PETERFEAYEZ-PERO/Smart-Modular-adjustable-DC-PSU/Images gallary/3d pervious images/Screenshot 2026-06-13 041023.png

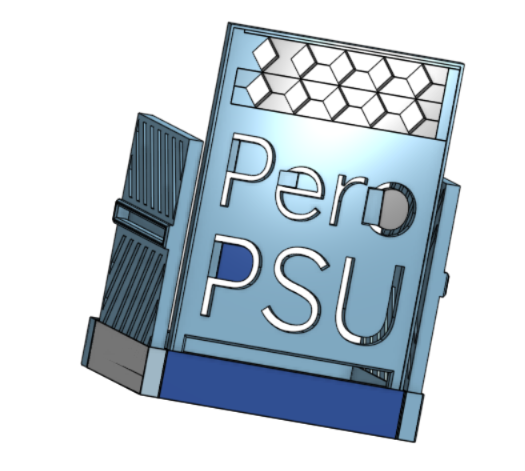
Images gallary/3d pervious images/Screenshot 2026-06-13 041023.png
