PETERFEAYEZ-PERO/Smart-Modular-adjustable-DC-PSU/Images gallary/3d pervious images/Screenshot 2026-06-12 073009.png

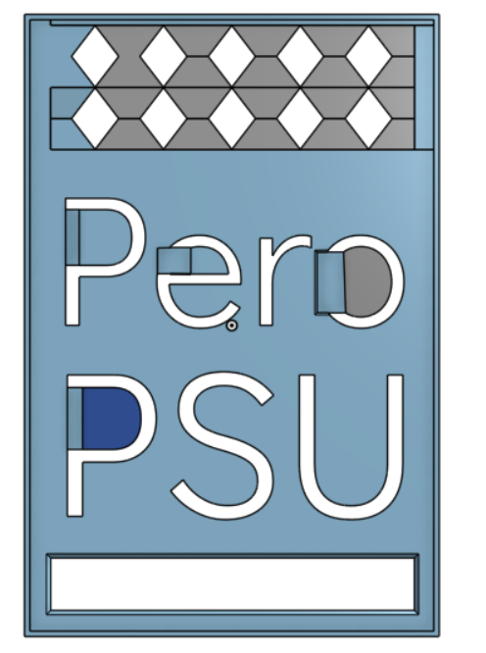
Images gallary/3d pervious images/Screenshot 2026-06-12 073009.png
