PETERFEAYEZ-PERO/Smart-Modular-adjustable-DC-PSU/Images gallary/PCB pervious versions images/Screenshot 2026-05-29 034604.png

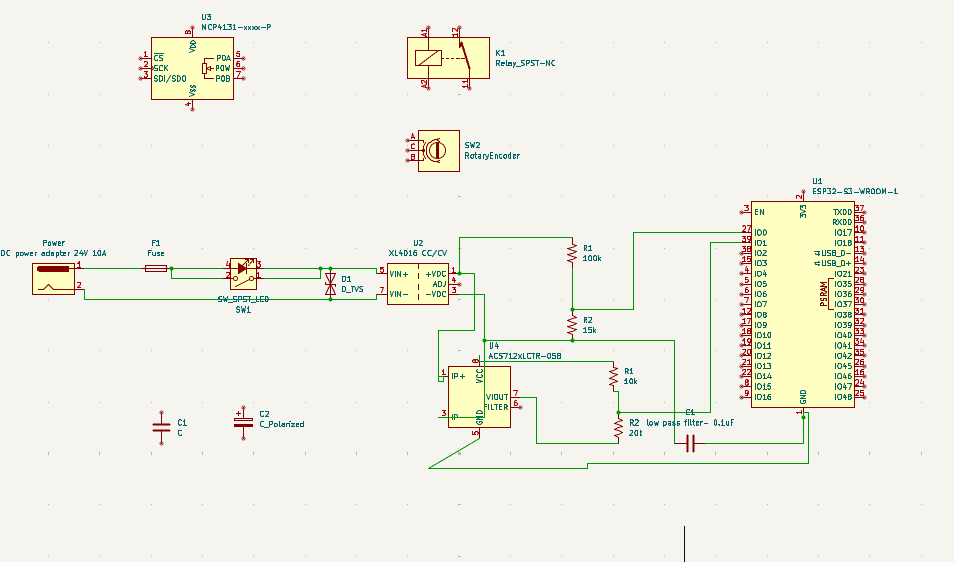
Images gallary/PCB pervious versions images/Screenshot 2026-05-29 034604.png
