PETERFEAYEZ-PERO/Smart-Modular-adjustable-DC-PSU/Images gallary/PCB pervious versions images/Screenshot 2026-06-07 052628 - Copy.png

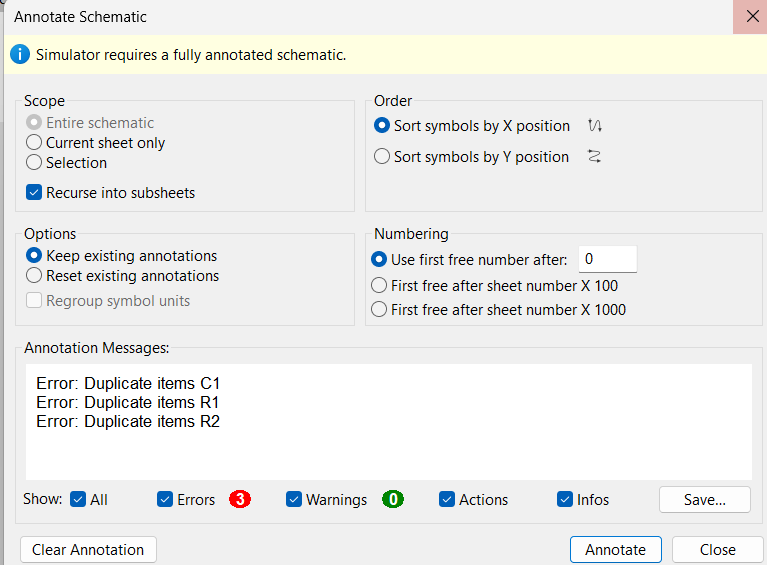
Images gallary/PCB pervious versions images/Screenshot 2026-06-07 052628 - Copy.png
