PETERFEAYEZ-PERO/Smart-Modular-adjustable-DC-PSU/Images gallary/PCB pervious versions images/Screenshot 2026-06-13 090125.png

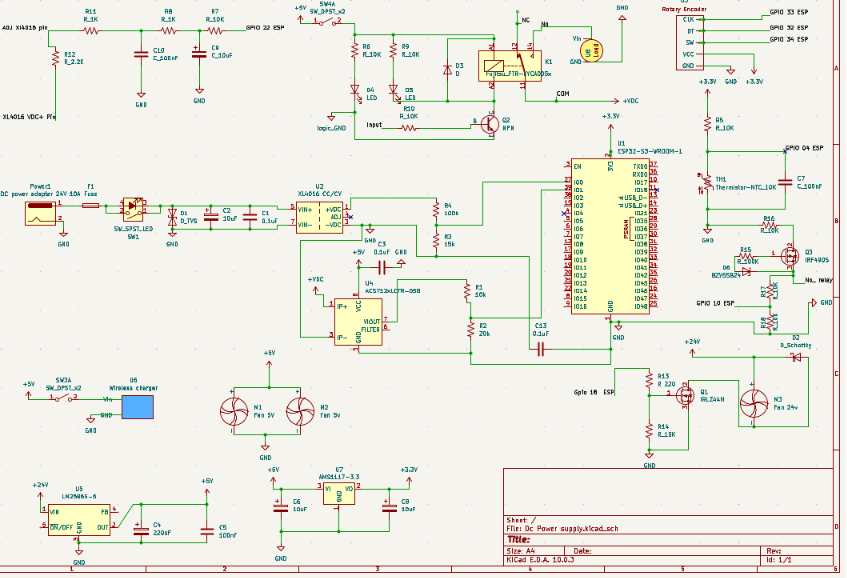
Images gallary/PCB pervious versions images/Screenshot 2026-06-13 090125.png
