PETERFEAYEZ-PERO/Smart-Modular-adjustable-DC-PSU/PCB/USB HUP/USB Hup.kicad_pcb

## KiCad design ereader/audio_headphones.kicad_sch

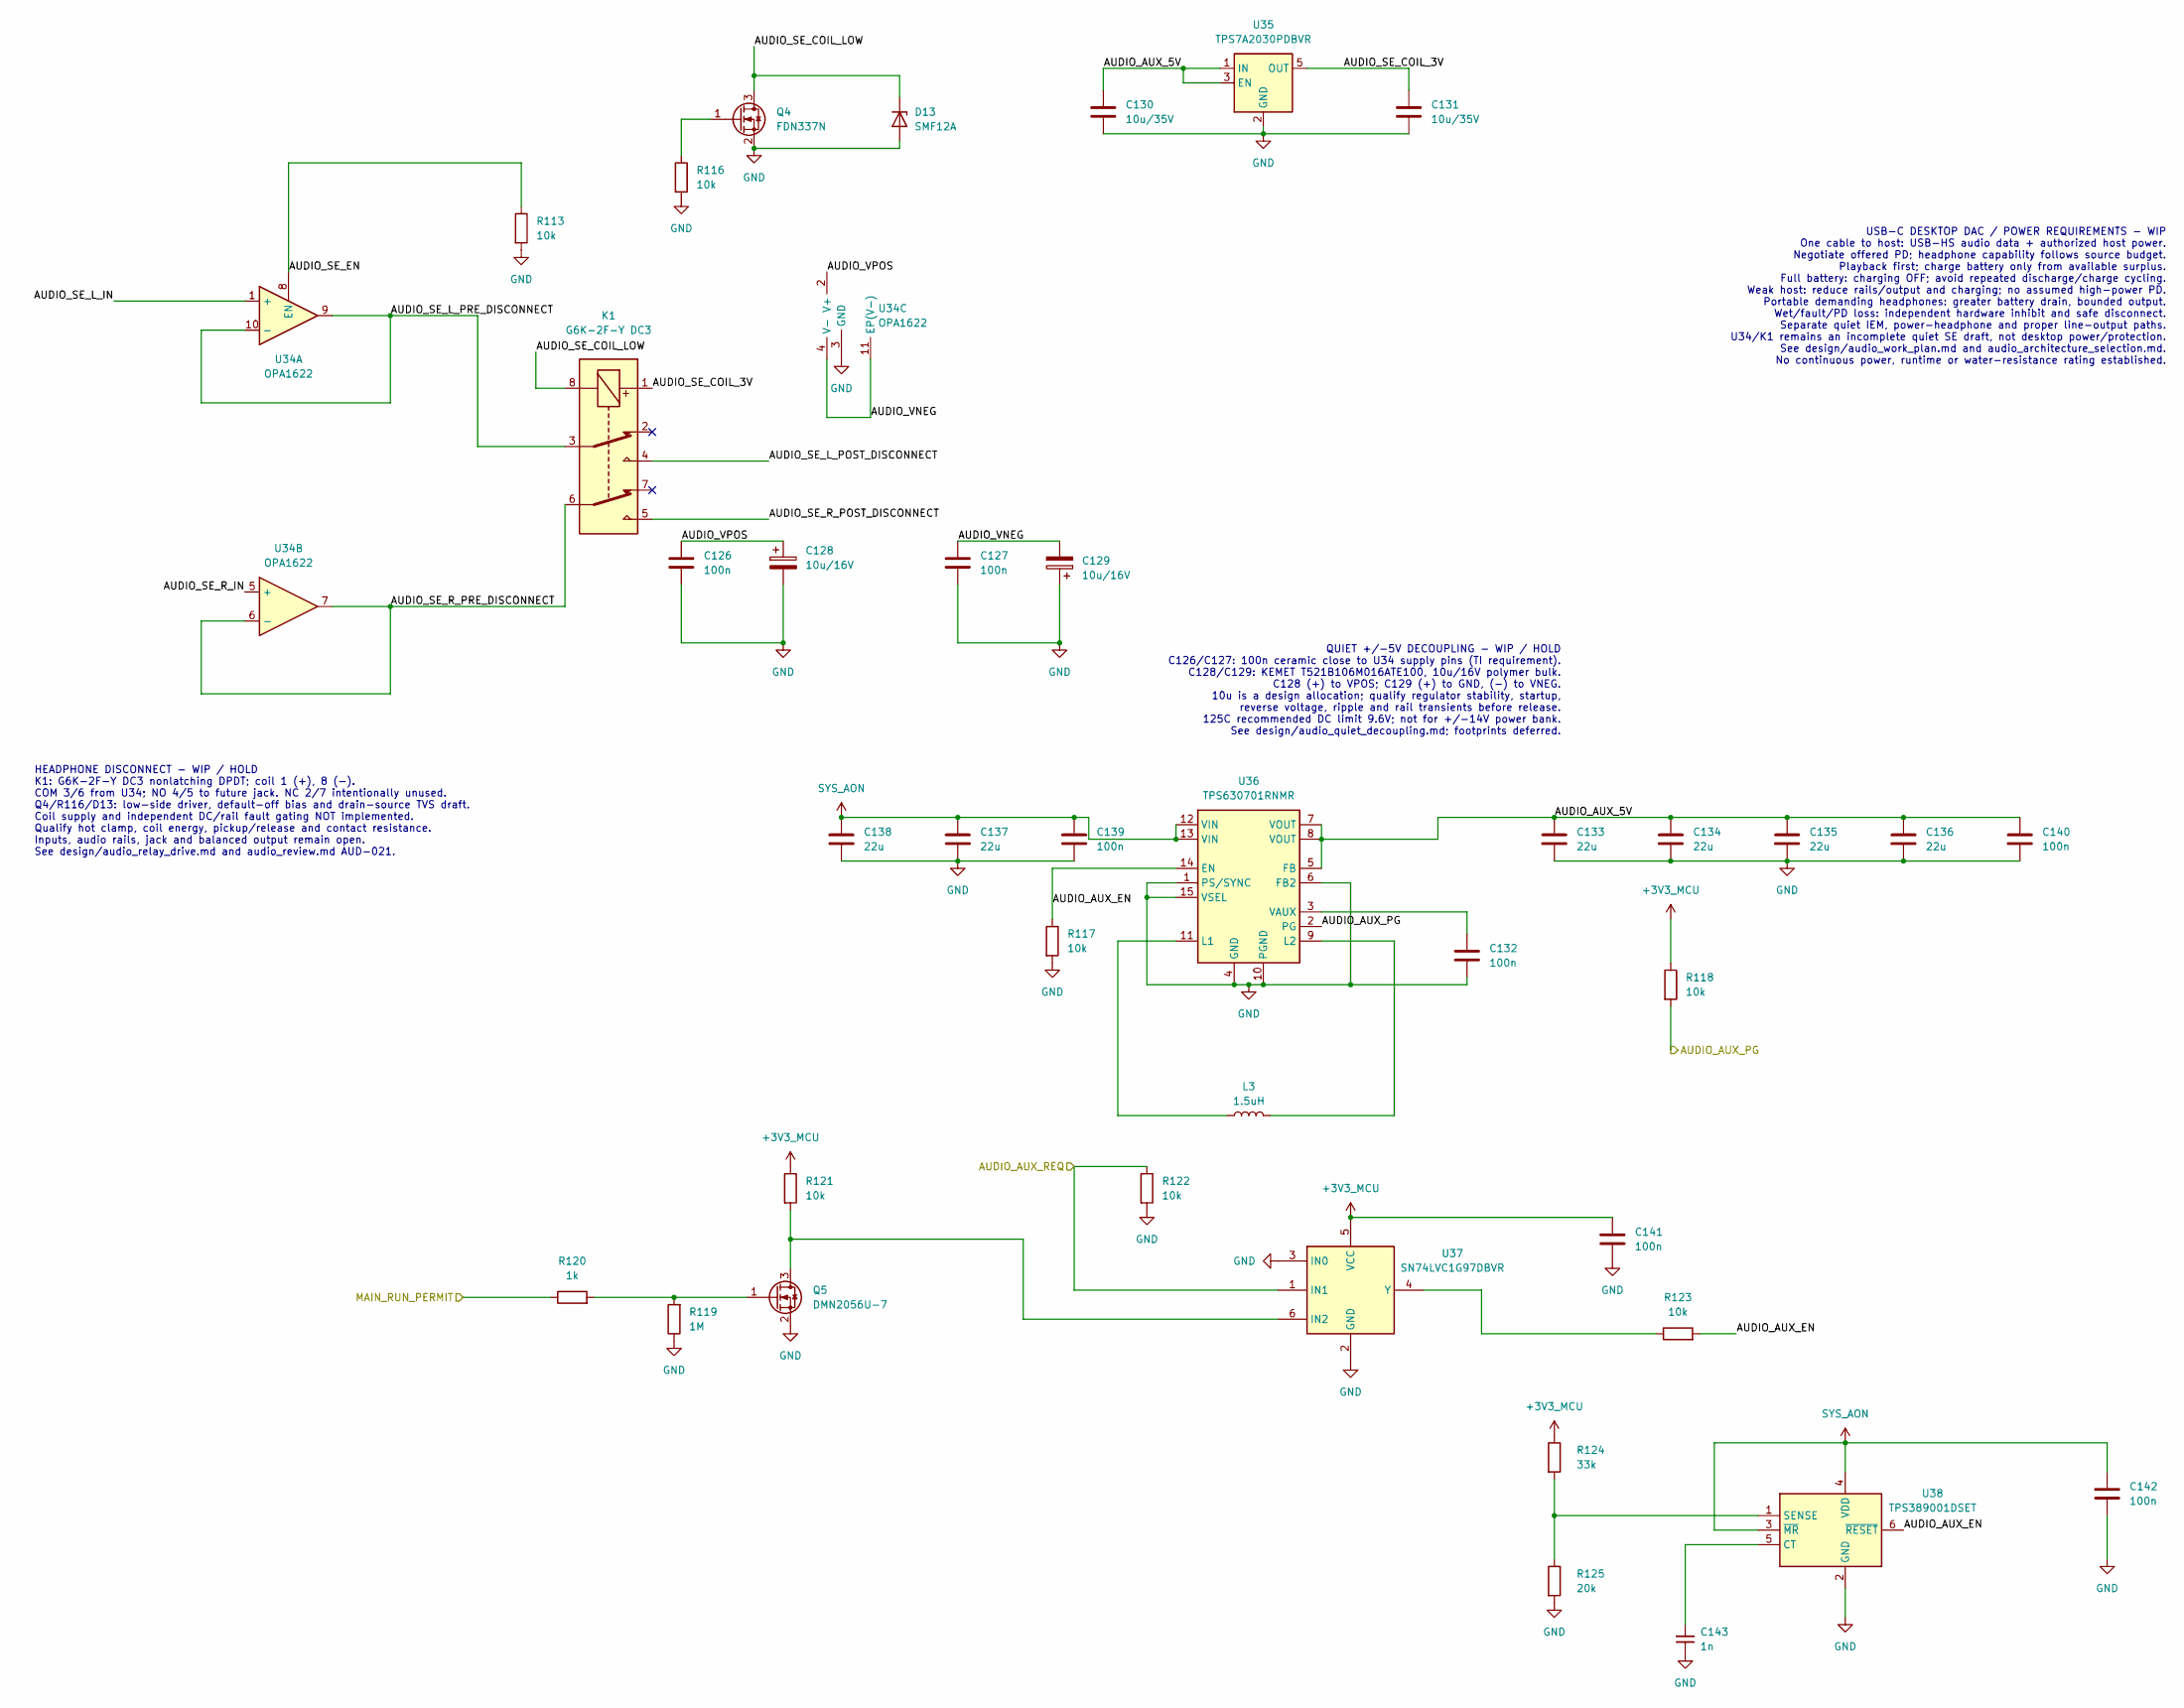
[picture p48: schematic audio_headphones.kicad_sch]

Parts:
C126, C127, C132, C139, C140, C141, C142: 100n; Manufacturer_Part_Number C1608X7R1H104K080AA
C128, C129: 10u/16V; Manufacturer_Part_Number T521B106M016ATE100
C130, C131: 10u/35V
C133, C134, C135, C136, C137, C138: 22u; Manufacturer_Part_Number CL32B226MOJNNNE; DigiKey_Part_Number 1276-3395-1-ND
C143: 1n; Manufacturer_Part_Number C1608NP01H102J080AA; DigiKey_Part_Number 445-14055-1-ND
D13: SMF12A; Manufacturer_Part_Number SMF12A; DigiKey_Part_Number F5747CT-ND
K1: G6K-2F-Y DC3; Manufacturer_Part_Number G6K-2F-Y DC3; DigiKey_Part_Number 39-G6K-2F-YDC3-ND
L3: 1.5uH; Manufacturer_Part_Number XGL4020-152MEC
Q4: FDN337N; Manufacturer_Part_Number FDN337N; DigiKey_Part_Number FDN337NCT-ND
Q5: DMN2056U-7; SOT-23; Manufacturer_Part_Number DMN2056U-7; DigiKey_Part_Number DMN2056U-7DICT-ND
R113, R116, R117, R118, R121, R122, R123: 10k; Manufacturer_Part_Number RC0603FR-0710KL; DigiKey_Part_Number 311-10.0KHRCT-ND
R119: 1M; Manufacturer_Part_Number RC0603FR-071ML; DigiKey_Part_Number 311-1.00MHRCT-ND
R120: 1k; Manufacturer_Part_Number RC0603FR-071KL; DigiKey_Part_Number 311-1.00KHRCT-ND
R124: 33k; Manufacturer_Part_Number ERA-6ARW333V; DigiKey_Part_Number P33KBSCT-ND
R125: 20k; Manufacturer_Part_Number RG1608N-203-W-T1; DigiKey_Part_Number RG16N20.0KWCT-ND
U34: OPA1622; Manufacturer_Part_Number OPA1622IDRCR; DigiKey_Part_Number 296-45038-1-ND
U35: TPS7A2030PDBVR
U36: TPS630701RNMR
U37: SN74LVC1G97DBVR; Manufacturer_Part_Number SN74LVC1G97DBVR; DigiKey_Part_Number 296-15581-1-ND
U38: TPS389001DSET; Manufacturer_Part_Number TPS389001DSET; DigiKey_Part_Number 296-44489-1-ND

Connections:
+3V3_MCU: C141.1, R118.1, R121.1, R124.1, U37.5 (VCC)
AUDIO_AUX_5V: C130.1, C133.1, C134.1, C135.1, C136.1, C140.1, U35.1 (IN), U35.3 (EN), U36.5 (FB), U36.7 (VOUT), U36.8 (VOUT)
AUDIO_AUX_EN: R117.1, R123.2, U36.14 (EN), U38.6 (~RESET)
AUDIO_AUX_PG: R118.2, U36.2 (PG)
AUDIO_AUX_REQ: R122.1, U37.1 (IN1)
AUDIO_SE_COIL_3V: C131.1, K1.1, U35.5 (OUT)
AUDIO_SE_COIL_LOW: D13.1 (K), K1.8, Q4.3 (D)
AUDIO_SE_EN: R113.1, U34.8 (EN)
AUDIO_SE_L_IN: U34.1 (+)
AUDIO_SE_L_POST_DISCONNECT: K1.4
AUDIO_SE_L_PRE_DISCONNECT: K1.3, U34.9, U34.10 (-)
AUDIO_SE_R_IN: U34.5 (+)
AUDIO_SE_R_POST_DISCONNECT: K1.5
AUDIO_SE_R_PRE_DISCONNECT: K1.6, U34.6 (-), U34.7
AUDIO_VNEG: C127.1, C129.2, U34.4 (V-), U34.11 (EP(V-))
AUDIO_VPOS: C126.1, C128.1, U34.2 (V+)
GND: C126.2, C127.2, C128.2, C129.1, C130.2, C131.2, C132.2, C133.2, C134.2, C135.2, C136.2, C137.2, C138.2, C139.2, C140.2, C141.2, C142.2, C143.1, D13.2 (A), Q4.2 (S), Q5.2 (S), R113.2, R116.2, R117.2, R119.1, R122.2, R125.2, U34.3 (GND), U35.2 (GND), U36.1 (PS/SYNC), U36.4 (GND), U36.6 (FB2), U36.10 (PGND), U36.15 (VSEL), U37.2 (GND), U37.3 (IN0), U38.2 (GND)
MAIN_RUN_PERMIT: R120.1
unnamed: C132.1, U36.3 (VAUX)
unnamed: C143.2, U38.5 (CT)
unnamed: L3.1, U36.11 (L1)
unnamed: L3.2, U36.9 (L2)
unnamed: Q4.1 (G), R116.1
unnamed: Q5.1 (G), R119.2, R120.2
unnamed: Q5.3 (D), R121.2, U37.6 (IN2)
unnamed: R123.1, U37.4 (Y)
unnamed: R124.2, R125.1, U38.1 (SENSE)
SYS_AON: C137.1, C138.1, C139.1, C142.1, U36.12 (VIN), U36.13 (VIN), U38.3 (~MR), U38.4 (VDD)

Notes on the sheet:
HEADPHONE DISCONNECT - WIP / HOLD K1: G6K-2F-Y DC3 nonlatching DPDT; coil 1 (+), 8 (-). COM 3/6 from U34; NO 4/5 to future jack. NC 2/7 intentionally unused. Q4/R116/D13: low-side driver, default-off bias and drain-source TVS draft. Coil supply and independent DC/rail fault gating NOT implemented. 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
QUIET +/-5V DECOUPLING - WIP / HOLD C126/C127: 100n ceramic close to U34 supply pins (TI requirement). C128/C129: KEMET T521B106M016ATE100, 10u/16V polymer bulk. C128 (+) to VPOS; C129 (+) to GND, (-) to VNEG. 10u is a design allocation; qualify regulator stability, startup, reverse voltage, ripple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
USB-C DESKTOP DAC / POWER REQUIREMENTS - WIP One cable to host: USB-HS audio data + authorized host power. Negotiate offered PD; headphone capability follows source budget. Playback first; charge battery only from available surplus. Full battery: charging OFF; avoid repeated discharge/charge cyclin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
