PETERFEAYEZ-PERO/Smart-Modular-adjustable-DC-PSU/PCB/USB HUP/USB Hup.kicad_pcb

## KiCad design ereader/camera.kicad_sch

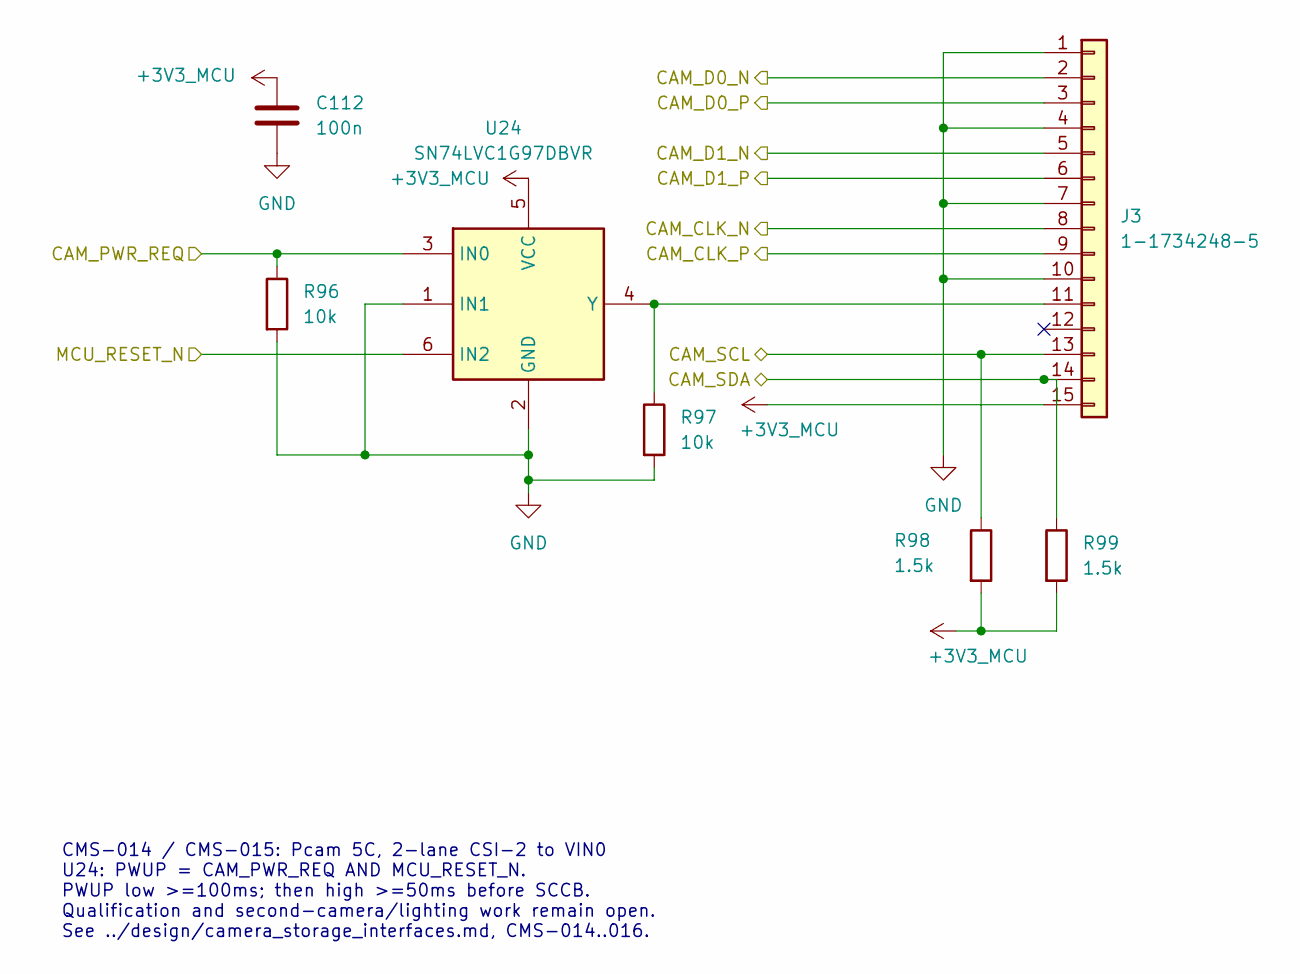
[picture p49: schematic camera.kicad_sch]

Parts:
C112: 100n; Manufacturer_Part_Number C1608X7R1H104K080AA; DigiKey_Part_Number 445-1314-1-ND
J3: 1-1734248-5; Manufacturer_Part_Number 1-1734248-5; DigiKey_Part_Number A101418CT-ND
R96, R97: 10k; Manufacturer_Part_Number RC0603FR-0710KL; DigiKey_Part_Number 311-10.0KHRCT-ND
R98, R99: 1.5k; Manufacturer_Part_Number RC0603FR-071K5L; DigiKey_Part_Number 311-1.50KHRCT-ND
U24: SN74LVC1G97DBVR; Manufacturer_Part_Number SN74LVC1G97DBVR; DigiKey_Part_Number 296-15581-1-ND

Connections:
+3V3_MCU: C112.1, J3.15, R98.2, R99.2, U24.5 (VCC)
CAM_CLK_N: J3.8
CAM_CLK_P: J3.9
CAM_D0_N: J3.2
CAM_D0_P: J3.3
CAM_D1_N: J3.5
CAM_D1_P: J3.6
CAM_PWR_REQ: R96.1, U24.3 (IN0)
CAM_SCL: J3.13, R98.1
CAM_SDA: J3.14, R99.1
GND: C112.2, J3.1, J3.4, J3.7, J3.10, R96.2, R97.2, U24.1 (IN1), U24.2 (GND)
MCU_RESET_N: U24.6 (IN2)
unnamed: J3.11, R97.1, U24.4 (Y)

Notes on the sheet:
CMS-014 / CMS-015: Pcam 5C, 2-lane CSI-2 to VIN0 U24: PWUP = CAM_PWR_REQ AND MCU_RESET_N. PWUP low >=100ms; then high >=50ms before SCCB. Qualification and second-camera/lighting work remain open. See ../design/camera_storage_interfaces.md, CMS-014..016.
