PETERFEAYEZ-PERO/Smart-Modular-adjustable-DC-PSU/PCB/USB HUP/USB Hup.kicad_pcb

## KiCad design ereader/main_3v3_supply.kicad_sch

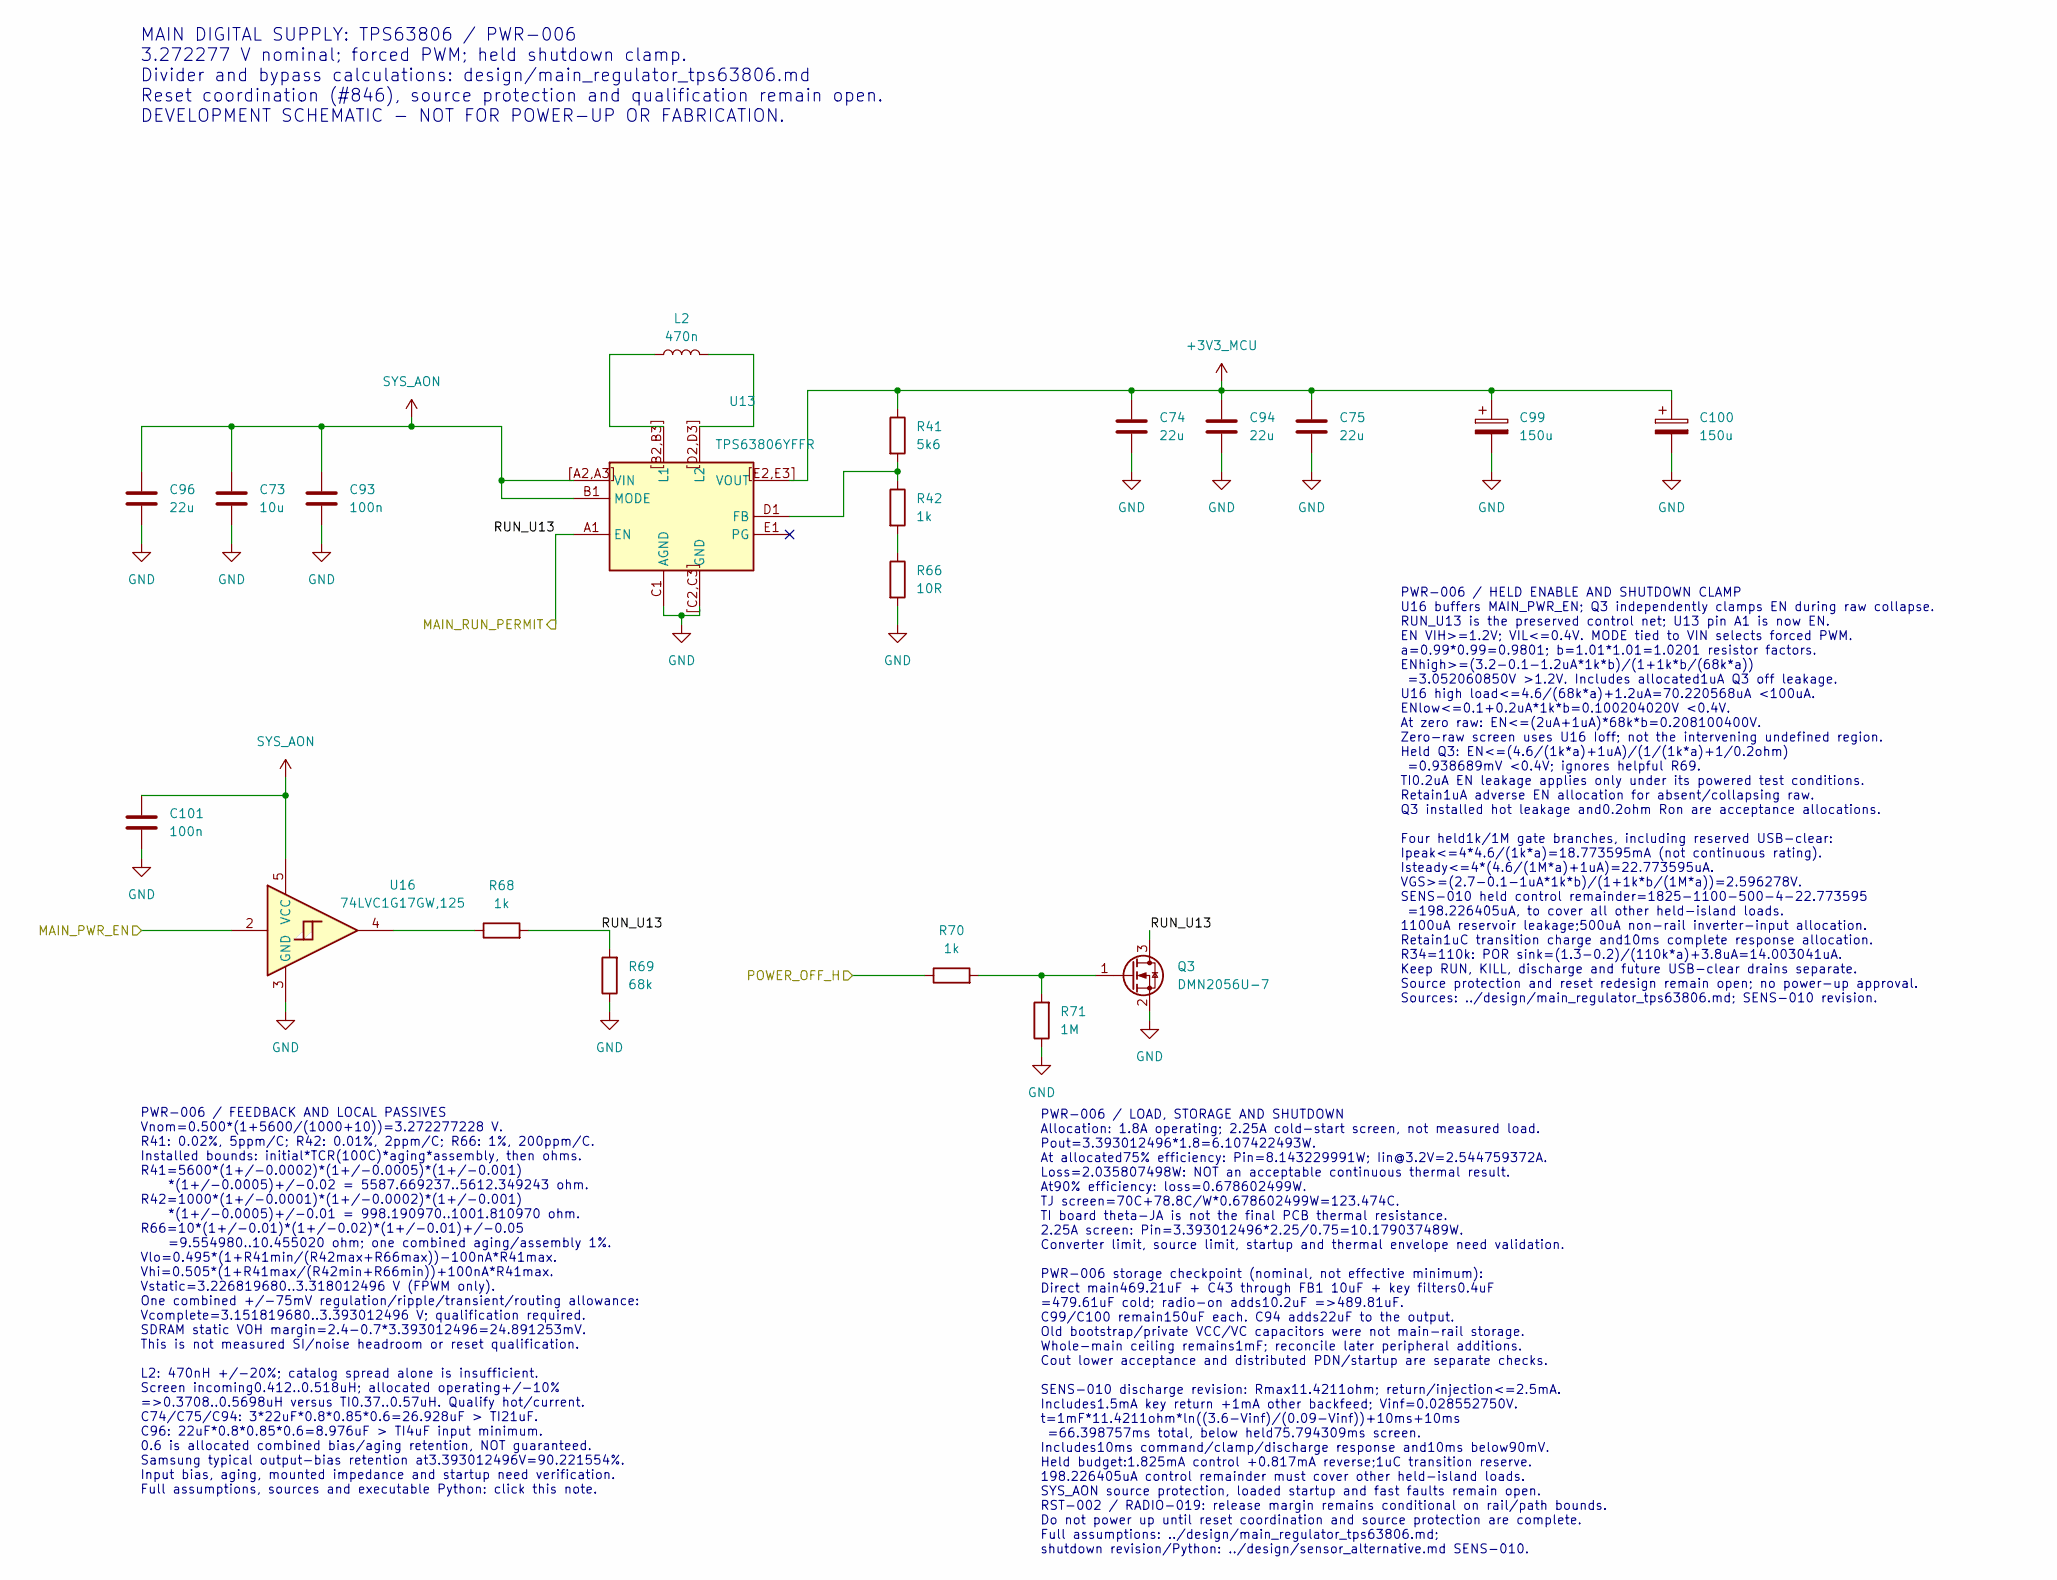
[picture p50: schematic main_3v3_supply.kicad_sch]

Parts:
C73: 10u; Manufacturer_Part_Number C3216X7R1V106K160AC; DigiKey_Part_Number 445-14799-1-ND
C74, C75, C94, C96: 22u; Manufacturer_Part_Number CL32B226MOJNNNE; DigiKey_Part_Number 1276-3395-1-ND
C93, C101: 100n; Manufacturer_Part_Number C1608X7R1H104K080AA; DigiKey_Part_Number 445-1314-1-ND
C99, C100: 150u; Manufacturer_Part_Number EEF-JX0J151RF; DigiKey_Part_Number 10-EEF-JX0J151RFCT-ND
L2: 470n; Manufacturer_Part_Number XGL5020-471MEC; DigiKey_Part_Number 2457-XGL5020-471MEC-ND
Q3: DMN2056U-7; SOT-23; Manufacturer_Part_Number DMN2056U-7; DigiKey_Part_Number DMN2056U-7DICT-ND
R41: 5k6; Manufacturer_Part_Number RG2012V-562-P-T1; DigiKey_Part_Number 408-RG2012V-562-P-T1CT-ND
R42: 1k; Manufacturer_Part_Number RG2012L-102-L-T05; DigiKey_Part_Number 408-1631-1-ND
R66: 10R; Manufacturer_Part_Number RC0603FR-0710RL; DigiKey_Part_Number 311-10.0HRCT-ND
R68, R70: 1k; Manufacturer_Part_Number RC0603FR-071KL; DigiKey_Part_Number 311-1.00KHRCT-ND
R69: 68k; Manufacturer_Part_Number RC0603FR-0768KL; DigiKey_Part_Number 311-68.0KHRCT-ND
R71: 1M; Manufacturer_Part_Number RC0603FR-071ML; DigiKey_Part_Number 311-1.00MHRCT-ND
U13: TPS63806YFFR; Manufacturer_Part_Number TPS63806YFFR; DigiKey_Part_Number 296-TPS63806YFFRCT-ND
U16: 74LVC1G17GW,125; Manufacturer_Part_Number 74LVC1G17GW,125; DigiKey_Part_Number 1727-4117-1-ND

Connections:
+3V3_MCU: C74.1, C75.1, C94.1, C99.1, C100.1, R41.1, U13.[E2,E3] (VOUT)
GND: C73.2, C74.2, C75.2, C93.2, C94.2, C96.2, C99.2, C100.2, C101.2, Q3.2 (S), R66.2, R69.1, R71.1, U13.C1 (AGND), U13.[C2,C3] (GND), U16.3 (GND)
MAIN_PWR_EN: U16.2
MAIN_RUN_PERMIT: Q3.3 (D), R68.2, R69.2, U13.A1 (EN)
unnamed: L2.1, U13.[B2,B3] (L1)
unnamed: L2.2, U13.[D2,D3] (L2)
unnamed: Q3.1 (G), R70.2, R71.2
unnamed: R41.2, R42.1, U13.D1 (FB)
unnamed: R42.2, R66.1
unnamed: R68.1, U16.4
POWER_OFF_H: R70.1
SYS_AON: C73.1, C93.1, C96.1, C101.1, U13.B1 (MODE), U13.[A2,A3] (VIN), U16.5 (VCC)

Notes on the sheet:
PWR-006 / LOAD, STORAGE AND SHUTDOWN Allocation: 1.8A operating; 2.25A cold-start screen, not measured load. Pout=3.393012496*1.8=6.107422493W. At allocated75% efficiency: Pin=8.143229991W; Iin@3.2V=2.544759372A. Loss=2.035807498W: NOT an acceptable continuous thermal result. At90% efficiency: loss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
PWR-006 / HELD ENABLE AND SHUTDOWN CLAMP U16 buffers MAIN_PWR_EN; Q3 independently clamps EN during raw collapse. RUN_U13 is the preserved control net; U13 pin A1 is now EN. EN VIH>=1.2V; VIL<=0.4V. MODE tied to VIN selects forced PWM. a=0.99*0.99=0.9801; b=1.01*1.01=1.0201 resistor factors. ENhigh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
MAIN DIGITAL SUPPLY: TPS63806 / PWR-006 3.272277 V nominal; forced PWM; held shutdown clamp. Divider and bypass calculations: design/main_regulator_tps63806.md Reset coordination (#846), source protection and qualification remain open. DEVELOPMENT SCHEMATIC - NOT FOR POWER-UP OR FABRICATION.
PWR-006 / FEEDBACK AND LOCAL PASSIVES Vnom=0.500*(1+5600/(1000+10))=3.272277228 V. R41: 0.02%, 5ppm/C; R42: 0.01%, 2ppm/C; R66: 1%, 200ppm/C. Installed bounds: initial*TCR(100C)*aging*assembly, then ohms. R41=5600*(1+/-0.0002)*(1+/-0.0005)*(1+/-0.001) *(1+/-0.0005)+/-0.02 = 5587.669237..5612.349243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
