PETERFEAYEZ-PERO/Smart-Modular-adjustable-DC-PSU/PCB/USB HUP/USB Hup.kicad_pcb

## KiCad design ereader/mcu_core_power.kicad_sch

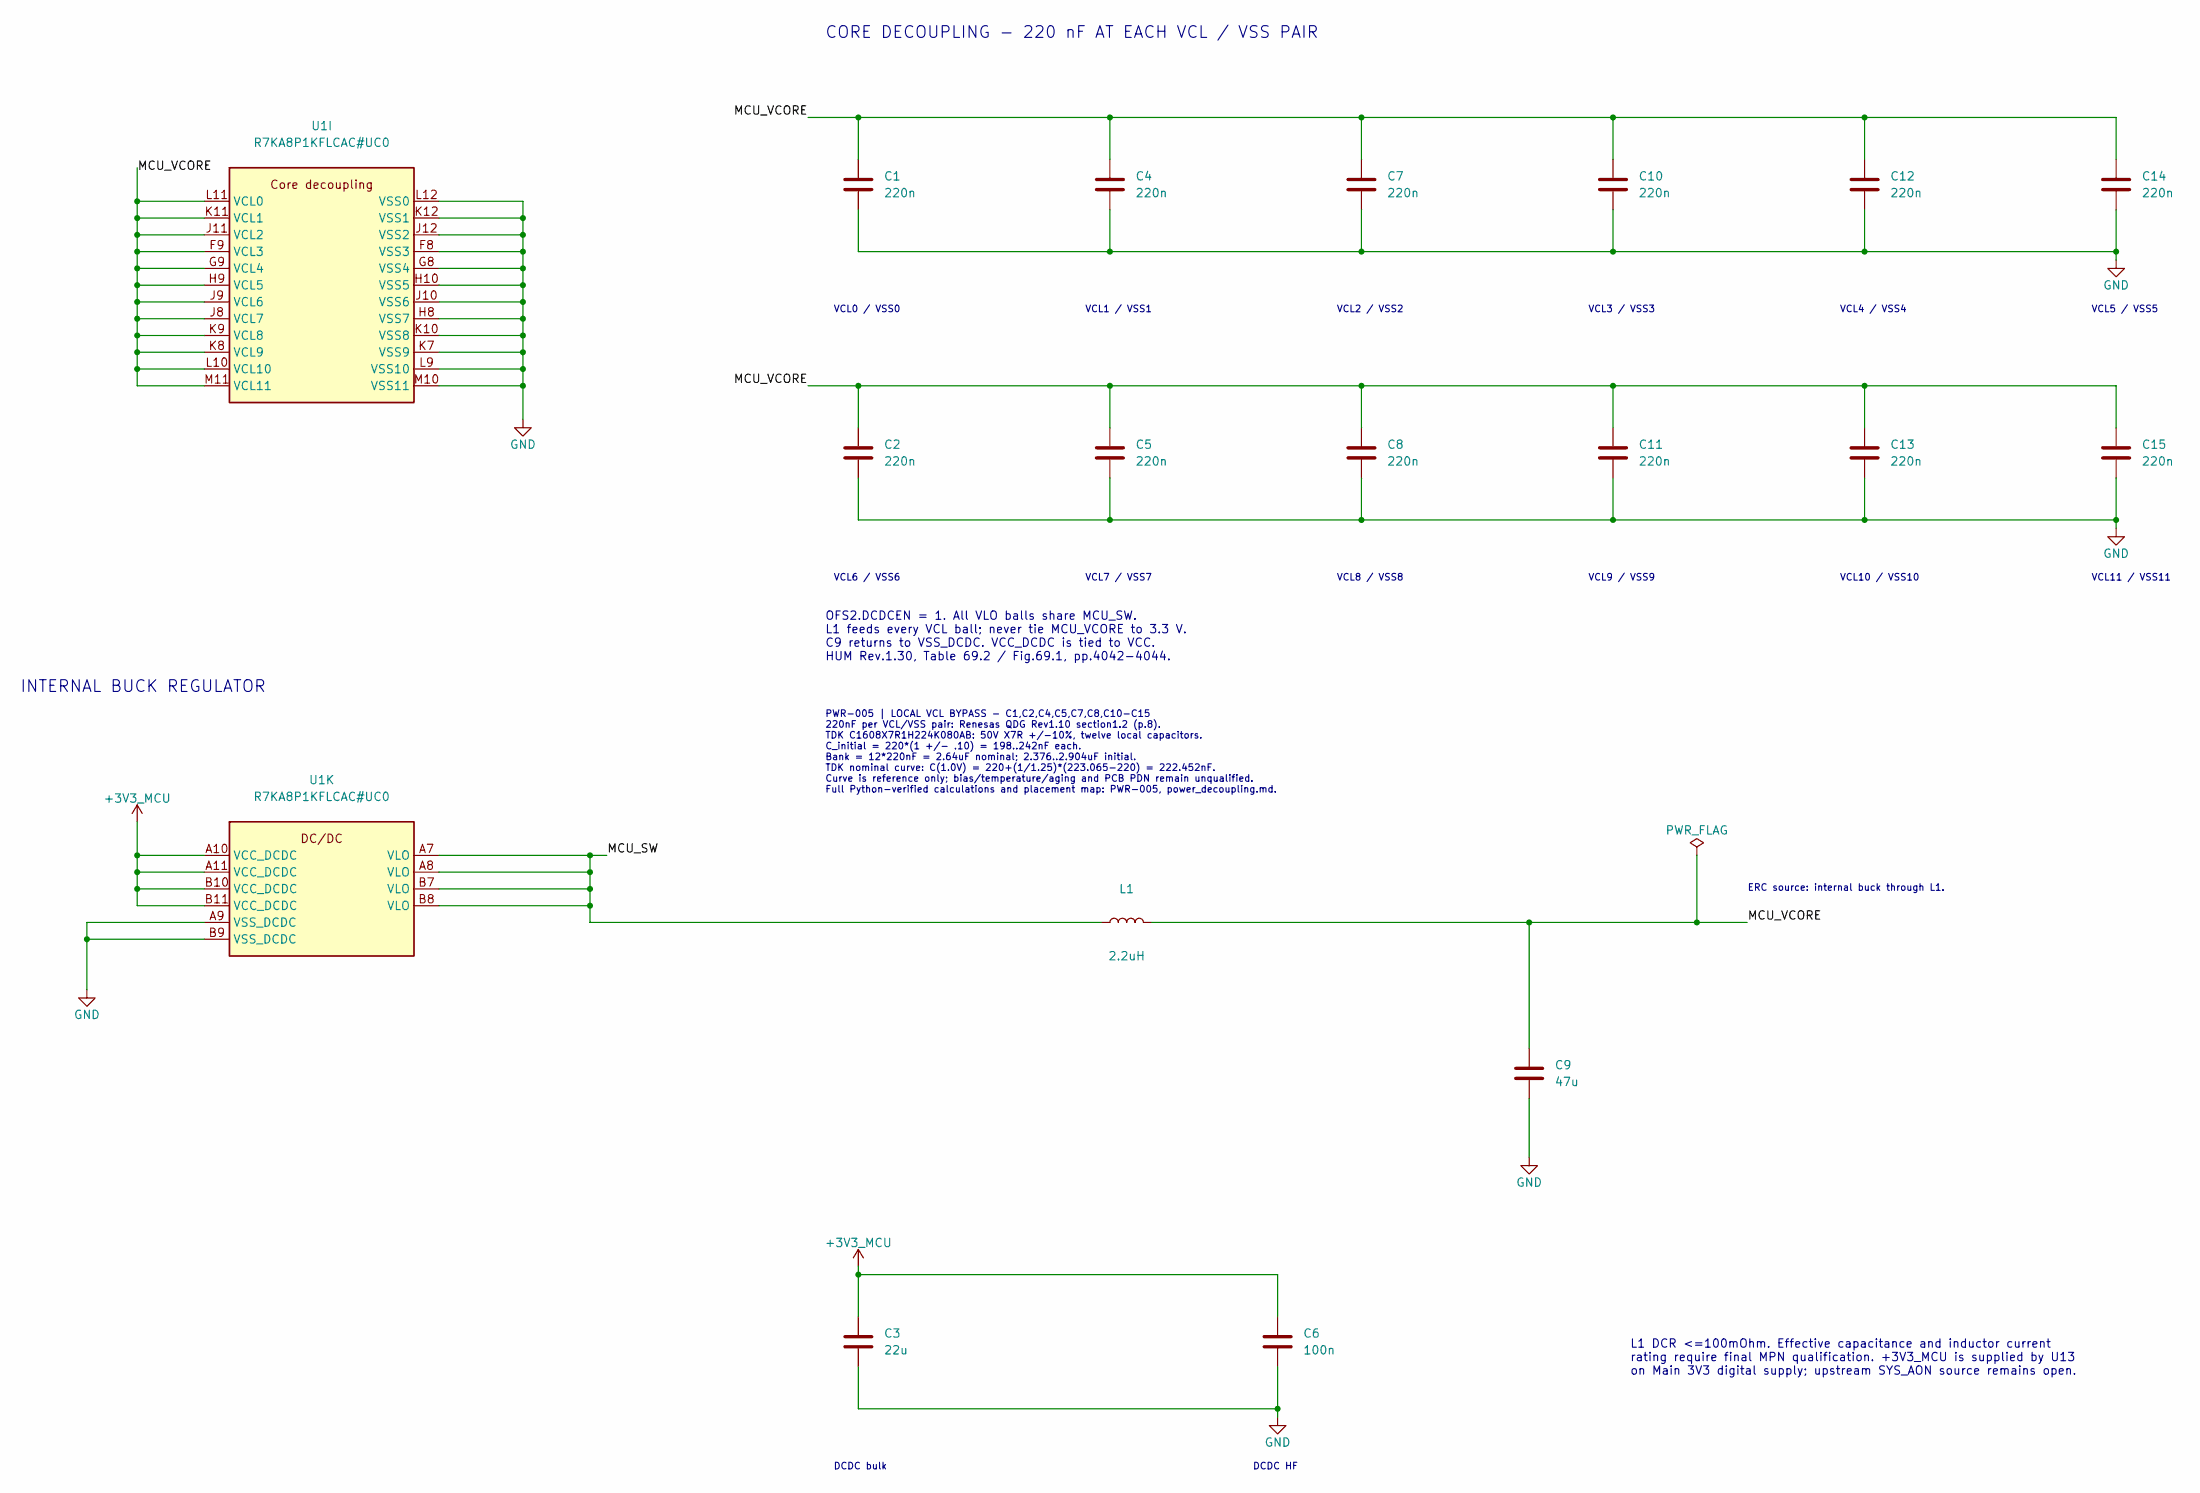
[picture p52: schematic mcu_core_power.kicad_sch]

Parts:
C1, C2, C4, C5, C7, C8, C10, C11, C12, C13, C14, C15: 220n; Manufacturer_Part_Number C1608X7R1H224K080AB; DigiKey_Part_Number 445-7408-1-ND
C3: 22u; Manufacturer_Part_Number GRM31CR70J226KE19L; DigiKey_Part_Number 490-6515-1-ND
C6: 100n; Manufacturer_Part_Number C1608X7R1H104K080AA; DigiKey_Part_Number 445-1314-1-ND
C9: 47u
L1: 2.2uH; Manufacturer_Part_Number SPM5020T-2R2M-LR; DigiKey_Part_Number 445-174497-1-ND
U1: R7KA8P1KFLCAC#UC0; BGA289C65P17X17_1200X1200X138; Mouser Part Number 968-R7KA8P1KFLCACUC0

Connections:
+3V3_MCU: C3.1, C6.1, U1.A10 (VCC_DCDC), U1.A11 (VCC_DCDC), U1.B10 (VCC_DCDC), U1.B11 (VCC_DCDC)
GND: C1.2, C2.2, C3.2, C4.2, C5.2, C6.2, C7.2, C8.2, C9.2, C10.2, C11.2, C12.2, C13.2, C14.2, C15.2, U1.A9 (VSS_DCDC), U1.B9 (VSS_DCDC), U1.F8 (VSS3), U1.G8 (VSS4), U1.H8 (VSS7), U1.H10 (VSS5), U1.J10 (VSS6), U1.J12 (VSS2), U1.K7 (VSS9), U1.K10 (VSS8), U1.K12 (VSS1), U1.L9 (VSS10), U1.L12 (VSS0), U1.M10 (VSS11)
MCU_SW: L1.1, U1.A7 (VLO), U1.A8 (VLO), U1.B7 (VLO), U1.B8 (VLO)
MCU_VCORE: C1.1, C2.1, C4.1, C5.1, C7.1, C8.1, C9.1, C10.1, C11.1, C12.1, C13.1, C14.1, C15.1, L1.2, U1.F9 (VCL3), U1.G9 (VCL4), U1.H9 (VCL5), U1.J8 (VCL7), U1.J9 (VCL6), U1.J11 (VCL2), U1.K8 (VCL9), U1.K9 (VCL8), U1.K11 (VCL1), U1.L10 (VCL10), U1.L11 (VCL0), U1.M11 (VCL11)

Notes on the sheet:
DCDC bulk
VCL2 / VSS2
VCL11 / VSS11
INTERNAL BUCK REGULATOR
VCL4 / VSS4
VCL3 / VSS3
VCL9 / VSS9
VCL8 / VSS8
VCL6 / VSS6
OFS2.DCDCEN = 1. All VLO balls share MCU_SW. L1 feeds every VCL ball; never tie MCU_VCORE to 3.3 V. C9 returns to VSS_DCDC. VCC_DCDC is tied to VCC. HUM Rev.1.30, Table 69.2 / Fig.69.1, pp.4042-4044.
VCL0 / VSS0
VCL10 / VSS10
L1 DCR <=100mOhm. Effective capacitance and inductor current rating require final MPN qualification. +3V3_MCU is supplied by U13 on Main 3V3 digital supply; upstream SYS_AON source remains open.
VCL1 / VSS1
PWR-005 | LOCAL VCL BYPASS - C1,C2,C4,C5,C7,C8,C10-C15 220nF per VCL/VSS pair: Renesas QDG Rev1.10 section1.2 (p.8). TDK C1608X7R1H224K080AB: 50V X7R +/-10%, twelve local capacitors. C_initial = 220*(1 +/- .10) = 198..242nF each. Bank = 12*220nF = 2.64uF nominal; 2.376..2.904uF initial. TDK nominal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
VCL5 / VSS5
VCL7 / VSS7
CORE DECOUPLING - 220 nF AT EACH VCL / VSS PAIR
DCDC HF
ERC source: internal buck through L1.
