PETERFEAYEZ-PERO/Smart-Modular-adjustable-DC-PSU/PCB/USB HUP/USB Hup.kicad_pcb

## KiCad design ereader/microsd.kicad_sch

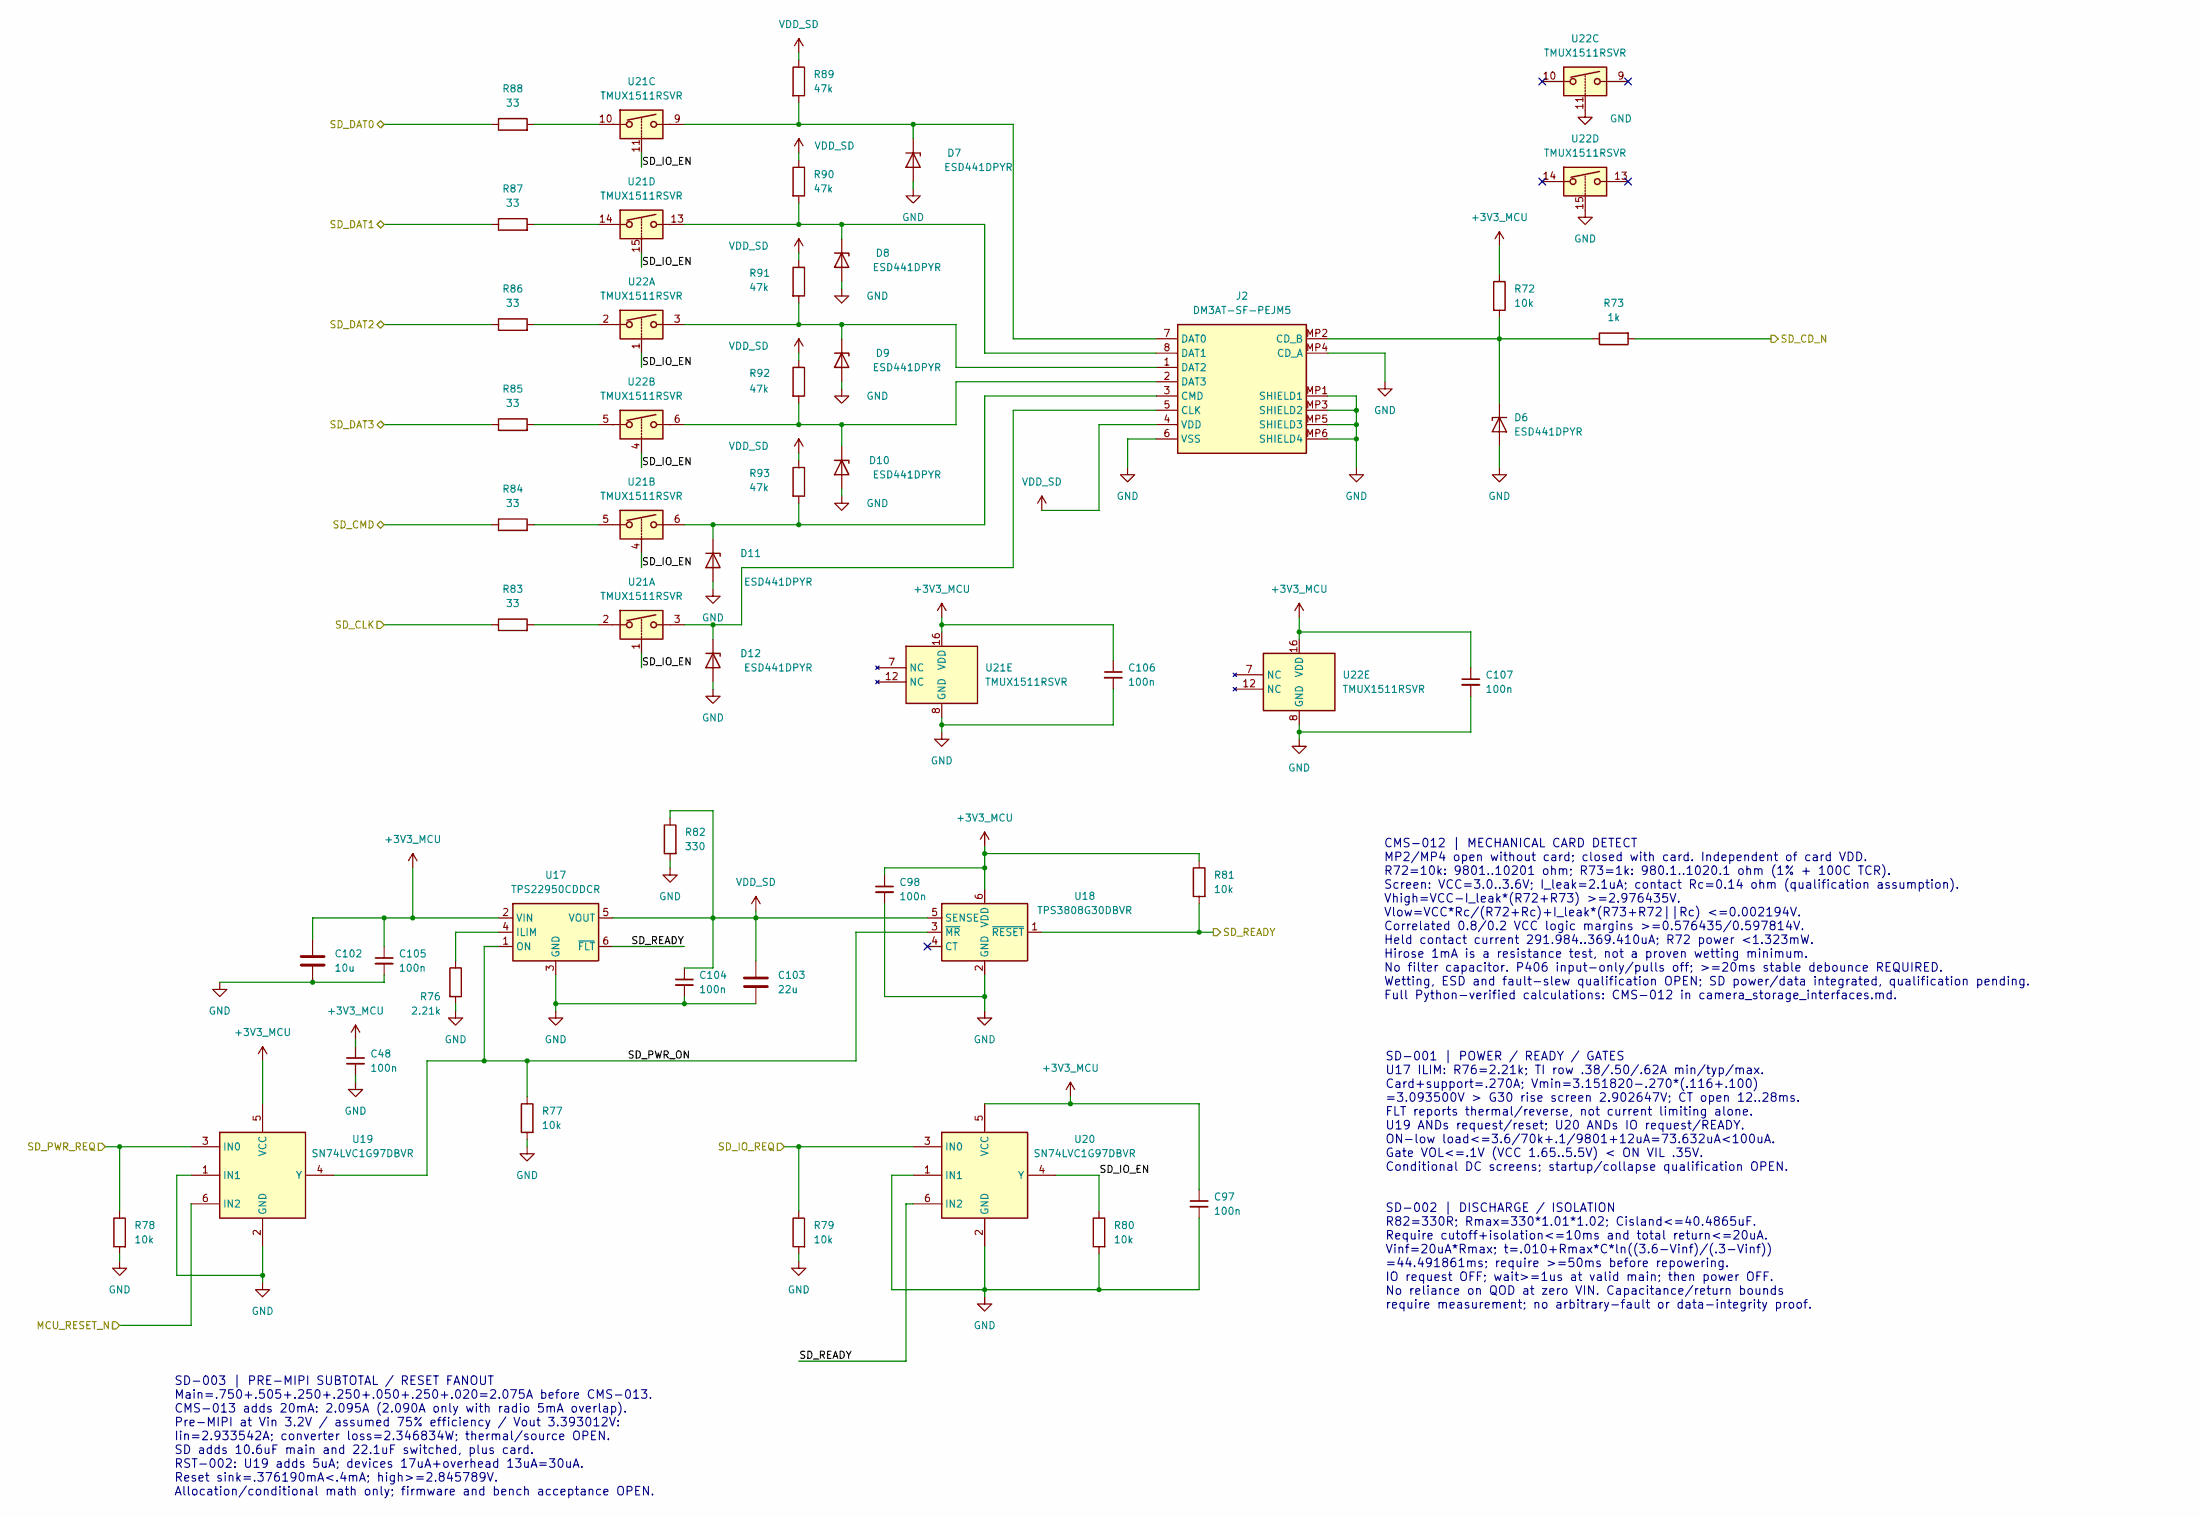
[picture p55: schematic microsd.kicad_sch]

Parts:
C48, C97, C98, C104, C105, C106, C107: 100n; Manufacturer_Part_Number C1608X7R1H104K080AA; DigiKey_Part_Number 445-1314-1-ND
C102: 10u; Manufacturer_Part_Number C3216X7R1V106K160AC; DigiKey_Part_Number 445-14799-1-ND
C103: 22u; Manufacturer_Part_Number CL32B226MOJNNNE; DigiKey_Part_Number 1276-3395-1-ND
D6, D7, D8, D9, D10, D11, D12: ESD441DPYR; Manufacturer_Part_Number ESD441DPYR; DigiKey_Part_Number 296-ESD441DPYRCT-ND
J2: DM3AT-SF-PEJM5; DM3ATSFPEJM5; Mouser Part Number 798-DM3AT-SF-PEJM5
R72, R77, R78, R79, R80, R81: 10k; Manufacturer_Part_Number RC0603FR-0710KL; DigiKey_Part_Number 311-10.0KHRCT-ND
R73: 1k; Manufacturer_Part_Number RC0603FR-071KL; DigiKey_Part_Number 311-1.00KHRCT-ND
R76: 2.21k; Manufacturer_Part_Number RC0603FR-072K21L; DigiKey_Part_Number 311-2.21KHRCT-ND
R82: 330; Manufacturer_Part_Number RC0603FR-07330RL; DigiKey_Part_Number 311-330HRCT-ND
R83, R84, R85, R86, R87, R88: 33; Manufacturer_Part_Number RC0603FR-0733RL; DigiKey_Part_Number 13-RC0603FR-0733RLCT-ND
R89, R90, R91, R92, R93: 47k; Manufacturer_Part_Number RC0603FR-0747KL; DigiKey_Part_Number 311-47.0KHRCT-ND
U17: TPS22950CDDCR; Manufacturer_Part_Number TPS22950CDDCR; DigiKey_Part_Number 296-TPS22950CDDCRCT-ND
U18: TPS3808G30DBVR; Manufacturer_Part_Number TPS3808G30DBVR; DigiKey_Part_Number 296-17194-1-ND
U19, U20: SN74LVC1G97DBVR; Manufacturer_Part_Number SN74LVC1G97DBVR; DigiKey_Part_Number 296-15581-1-ND
U21, U22: TMUX1511RSVR; Manufacturer_Part_Number TMUX1511RSVR; DigiKey_Part_Number 296-53443-1-ND

Connections:
+3V3_MCU: C48.1, C97.1, C98.1, C102.1, C105.1, C106.1, C107.1, R72.1, R81.1, U17.2 (VIN), U18.6 (VDD), U19.5 (VCC), U20.5 (VCC), U21.16 (VDD), U22.16 (VDD)
GND: C48.2, C97.2, C98.2, C102.2, C103.2, C104.2, C105.2, C106.2, C107.2, D6.2 (A), D7.2 (A), D8.2 (A), D9.2 (A), D10.2 (A), D11.2 (A), D12.2 (A), J2.6 (VSS), J2.MP1 (SHIELD1), J2.MP3 (SHIELD2), J2.MP4 (CD_A), J2.MP5 (SHIELD3), J2.MP6 (SHIELD4), R76.2, R77.2, R78.2, R79.2, R80.2, R82.2, U17.3 (GND), U18.2 (GND), U19.1 (IN1), U19.2 (GND), U20.1 (IN1), U20.2 (GND), U21.8 (GND), U22.8 (GND), U22.11, U22.15
MCU_RESET_N: U19.6 (IN2)
unnamed: D6.1 (K), J2.MP2 (CD_B), R72.2, R73.1
unnamed: D7.1 (K), J2.7 (DAT0), R89.2, U21.9
unnamed: D8.1 (K), J2.8 (DAT1), R90.2, U21.13
unnamed: D9.1 (K), J2.1 (DAT2), R91.2, U22.3
unnamed: D10.1 (K), J2.2 (DAT3), R92.2, U22.6
unnamed: D11.1 (K), J2.3 (CMD), R93.2, U21.6
unnamed: D12.1 (K), J2.5 (CLK), U21.3
unnamed: R76.1, U17.4 (ILIM)
unnamed: R83.2, U21.2
unnamed: R84.2, U21.5
unnamed: R85.2, U22.5
unnamed: R86.2, U22.2
unnamed: R87.2, U21.14
unnamed: R88.2, U21.10
SD_CD_N: R73.2
SD_CLK: R83.1
SD_CMD: R84.1
SD_DAT0: R88.1
SD_DAT1: R87.1
SD_DAT2: R86.1
SD_DAT3: R85.1
SD_IO_EN: R80.1, U20.4 (Y), U21.1, U21.4, U21.11, U21.15, U22.1, U22.4
SD_IO_REQ: R79.1, U20.3 (IN0)
SD_PWR_ON: R77.1, U17.1 (ON), U18.3 (~MR), U19.4 (Y)
SD_PWR_REQ: R78.1, U19.3 (IN0)
SD_READY: R81.2, U17.6 (~FLT), U18.1 (~RESET), U20.6 (IN2)
VDD_SD: C103.1, C104.1, J2.4 (VDD), R82.1, R89.1, R90.1, R91.1, R92.1, R93.1, U17.5 (VOUT), U18.5 (SENSE)

Notes on the sheet:
CMS-012 | MECHANICAL CARD DETECT MP2/MP4 open without card; closed with card. Independent of card VDD. R72=10k: 9801..10201 ohm; R73=1k: 980.1..1020.1 ohm (1% + 100C TCR). Screen: VCC=3.0..3.6V; I_leak=2.1uA; contact Rc=0.14 ohm (qualification assumption). Vhigh=VCC-I_leak*(R72+R73) >=2.976435V. Vl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
SD-003 | PRE-MIPI SUBTOTAL / RESET FANOUT Main=.750+.505+.250+.250+.050+.250+.020=2.075A before CMS-013. CMS-013 adds 20mA: 2.095A (2.090A only with radio 5mA overlap). Pre-MIPI at Vin 3.2V / assumed 75% efficiency / Vout 3.393012V: Iin=2.933542A; converter loss=2.346834W; thermal/source OPEN. SD a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
SD-001 | POWER / READY / GATES U17 ILIM: R76=2.21k; TI row .38/.50/.62A min/typ/max. Card+support=.270A; Vmin=3.151820-.270*(.116+.100) =3.093500V > G30 rise screen 2.902647V; CT open 12..28ms. FLT reports thermal/reverse, not current limiting alone. U19 ANDs request/reset; U20 ANDs IO request/READ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
SD-002 | DISCHARGE / ISOLATION R82=330R; Rmax=330*1.01*1.02; Cisland<=40.4865uF. Require cutoff+isolation<=10ms and total return<=20uA. Vinf=20uA*Rmax; t=.010+Rmax*C*ln((3.6-Vinf)/(.3-Vinf)) =44.491861ms; require >=50ms before repowering. IO request OFF; wait>=1us at valid main; then power OFF. No 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
