PETERFEAYEZ-PERO/Smart-Modular-adjustable-DC-PSU/PCB/USB HUP/USB Hup.kicad_pcb

## KiCad design ereader/orientation_sensor.kicad_sch

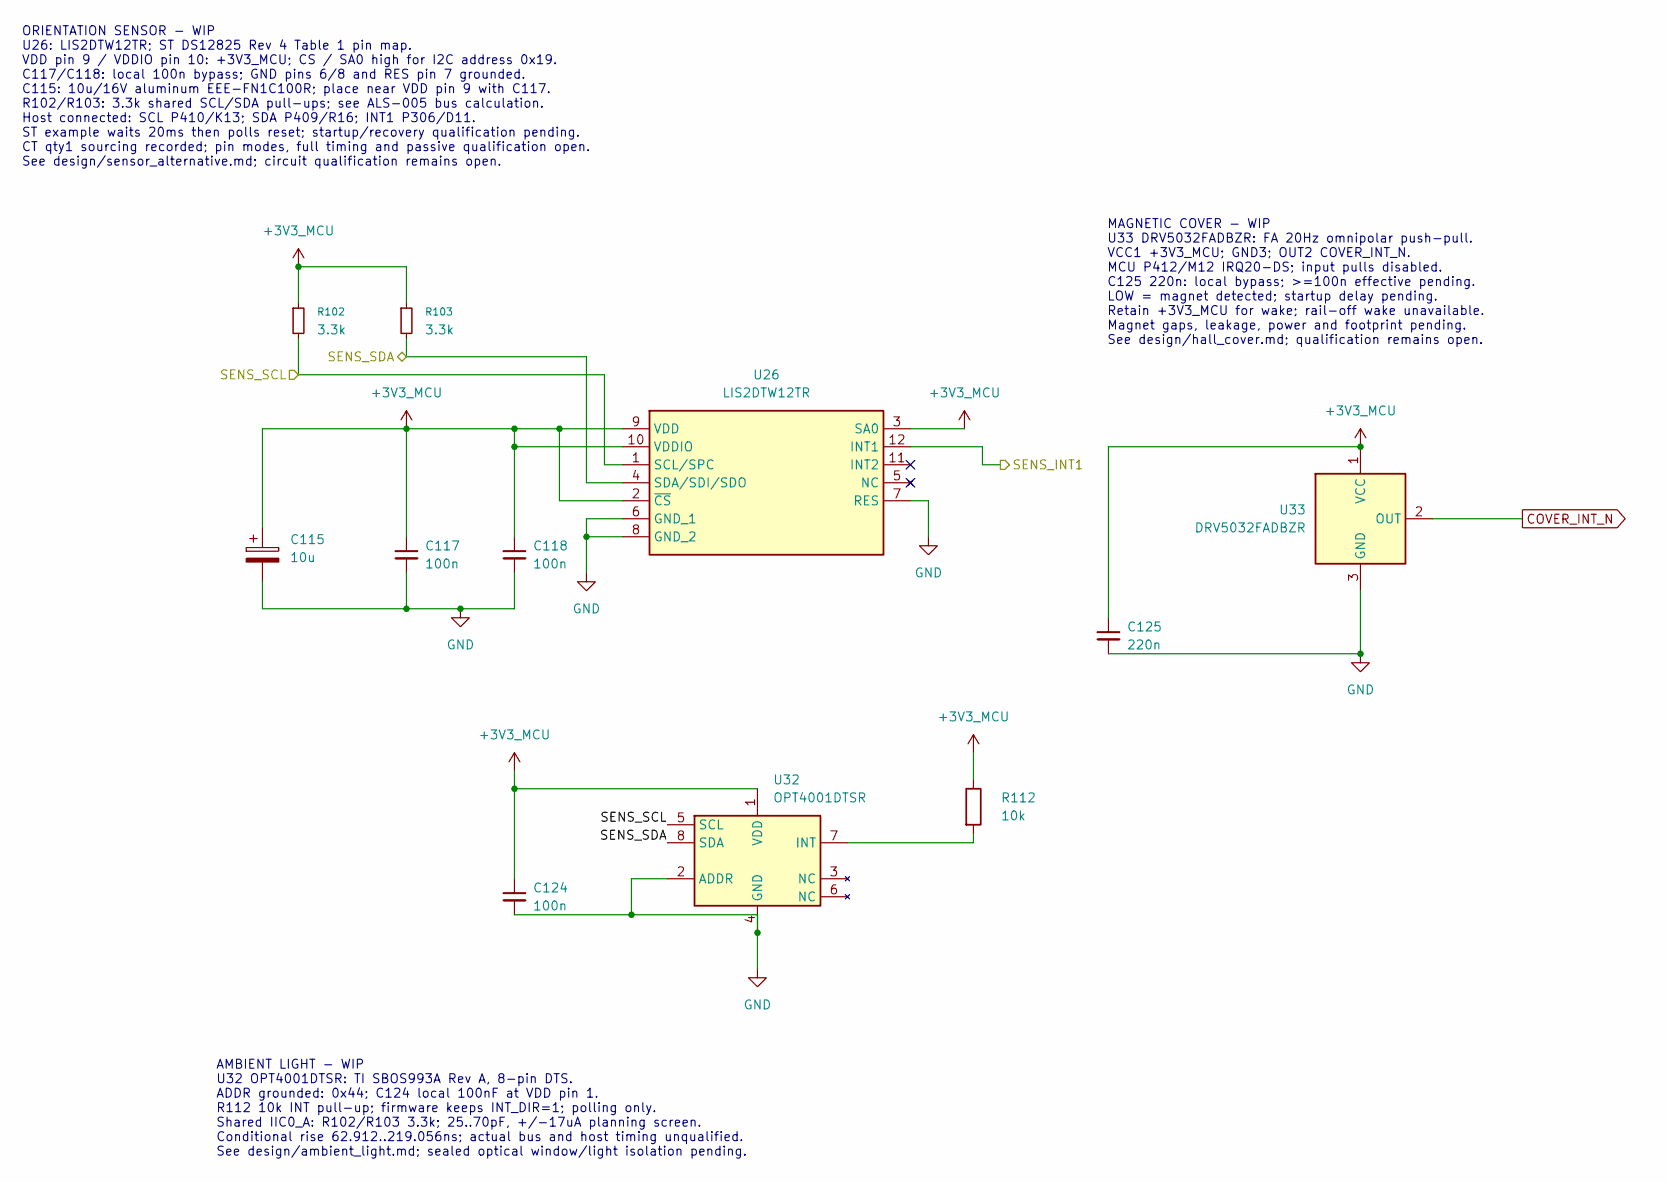
[picture p57: schematic orientation_sensor.kicad_sch]

Parts:
C115: 10u; MPN EEE-FN1C100R; DigiKey_Part_Number 10-EEE-FN1C100RCT-ND
C117, C118, C124: 100n; Manufacturer_Part_Number GRM188R72A104KA35D; DigiKey_Part_Number 490-3285-1-ND
C125: 220n; Manufacturer_Part_Number C1608X7R1H224K080AB; DigiKey_Part_Number 445-7408-1-ND
R102, R103: 3.3k; Manufacturer_Part_Number RC0603FR-073K3L; DigiKey_Part_Number 311-3.30KHRCT-ND
R112: 10k; Manufacturer_Part_Number RC0603FR-0710KL; DigiKey_Part_Number 311-10.0KHRCT-ND
U26: LIS2DTW12TR; Manufacturer_Part_Number LIS2DTW12TR; DigiKey_Part_Number 497-19047-1-ND
U32: OPT4001DTSR; Manufacturer_Part_Number OPT4001DTSR; DigiKey_Part_Number 296-OPT4001DTSRCT-ND
U33: DRV5032FADBZR; Manufacturer_Part_Number DRV5032FADBZR; DigiKey_Part_Number 296-47765-1-ND

Connections:
+3V3_MCU: C115.1, C117.1, C118.1, C124.1, C125.1, R102.1, R103.1, R112.1, U26.2 (~CS), U26.3 (SDO/SA0), U26.9 (VDD), U26.10 (VDDIO), U32.1 (VDD), U33.1 (VCC)
COVER_INT_N: U33.2 (OUT)
GND: C115.2, C117.2, C118.2, C124.2, C125.2, U26.6 (GND_1), U26.7 (RES), U26.8 (GND_2), U32.2 (ADDR), U32.4 (GND), U33.3 (GND)
unnamed: R112.2, U32.7 (INT)
SENS_INT1: U26.12 (INT1)
SENS_SCL: R102.2, U26.1 (SCL/SPC), U32.5 (SCL)
SENS_SDA: R103.2, U26.4 (SDA/SDI/SDO), U32.8 (SDA)

Notes on the sheet:
MAGNETIC COVER - WIP U33 DRV5032FADBZR: FA 20Hz omnipolar push-pull. VCC1 +3V3_MCU; GND3; OUT2 COVER_INT_N. MCU P412/M12 IRQ20-DS; input pulls disabled. C125 220n: local bypass; >=100n effective pending. LOW = magnet detected; startup delay pending. Retain +3V3_MCU for wake; rail-off wake unavailab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
AMBIENT LIGHT - WIP U32 OPT4001DTSR: TI SBOS993A Rev A, 8-pin DTS. ADDR grounded: 0x44; C124 local 100nF at VDD pin 1. R112 10k INT pull-up; firmware keeps INT_DIR=1; polling only. Shared IIC0_A: R102/R103 3.3k; 25..70pF, +/-17uA planning screen. Conditional rise 62.912..219.056ns; actual bus and h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
ORIENTATION SENSOR - WIP U26: LIS2DTW12TR; ST DS12825 Rev 4 Table 1 pin map. VDD pin 9 / VDDIO pin 10: +3V3_MCU; CS / SA0 high for I2C address 0x19. C117/C118: local 100n bypass; GND pins 6/8 and RES pin 7 grounded. C115: 10u/16V aluminum EEE-FN1C100R; place near VDD pin 9 with C117. R102/R103: 3.3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
