PETERFEAYEZ-PERO/Smart-Modular-adjustable-DC-PSU/PCB/USB HUP/USB Hup.kicad_pcb

## KiCad design ereader/power_button.kicad_sch

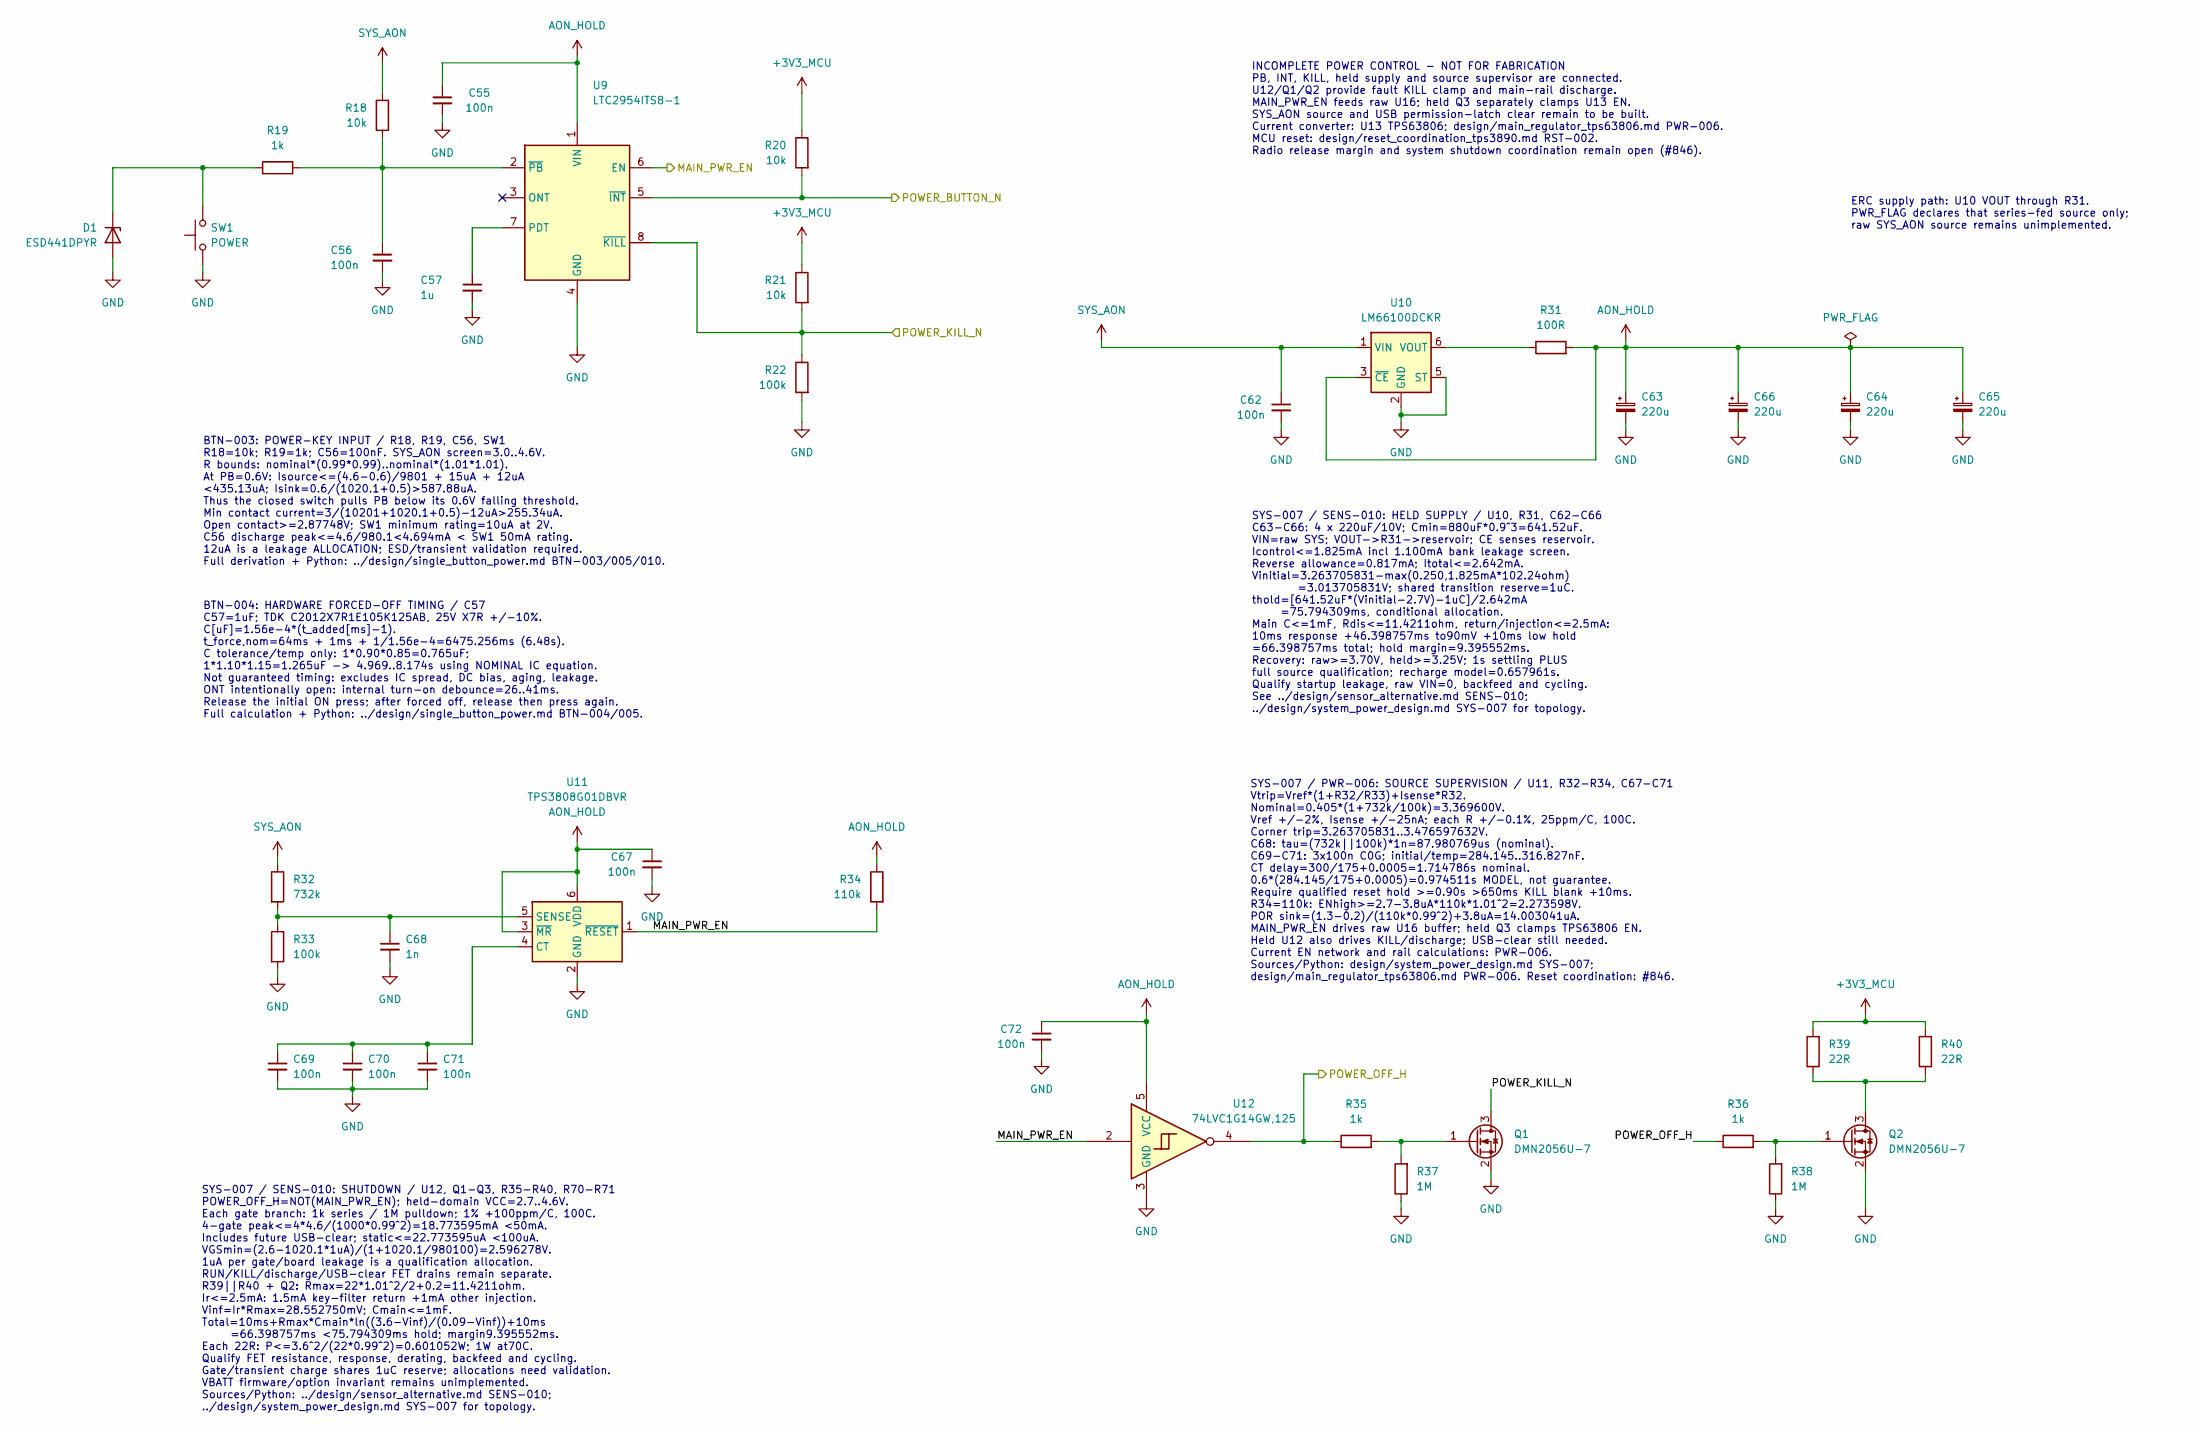
[picture p58: schematic power_button.kicad_sch]

Parts:
C55, C56, C62, C67, C72: 100n; Manufacturer_Part_Number C1608X7R1H104K080AA; DigiKey_Part_Number 445-1314-1-ND
C57: 1u; Manufacturer_Part_Number C2012X7R1E105K125AB; DigiKey_Part_Number 445-1354-1-ND
C63, C64, C65, C66: 220u; Manufacturer_Part_Number T491D227K010AT; DigiKey_Part_Number 399-8379-1-ND
C68: 1n; Manufacturer_Part_Number C1608NP01H102J080AA; DigiKey_Part_Number 445-14055-1-ND
C69, C70, C71: 100n; Manufacturer_Part_Number GRM31C5C1H104JA01K; DigiKey_Part_Number 490-8335-1-ND
D1: ESD441DPYR; Manufacturer_Part_Number ESD441DPYR; DigiKey_Part_Number 296-ESD441DPYRCT-ND
Q1, Q2: DMN2056U-7; SOT-23; Manufacturer_Part_Number DMN2056U-7; DigiKey_Part_Number DMN2056U-7DICT-ND
R18, R20, R21: 10k; Manufacturer_Part_Number RC0603FR-0710KL; DigiKey_Part_Number 311-10.0KHRCT-ND
R19, R35, R36: 1k; Manufacturer_Part_Number RC0603FR-071KL; DigiKey_Part_Number 311-1.00KHRCT-ND
R22: 100k; Manufacturer_Part_Number RC0603FR-07100KL; DigiKey_Part_Number 311-100KHRCT-ND
R31: 100R; Manufacturer_Part_Number RC2512FK-07100RL; DigiKey_Part_Number YAG3387CT-ND
R32: 732k; Manufacturer_Part_Number RT0805BRD07732KL; DigiKey_Part_Number YAG4938CT-ND
R33: 100k; Manufacturer_Part_Number TNPW0603100KBEEA; DigiKey_Part_Number TNP100KAACT-ND
R34: 110k; Manufacturer_Part_Number RC0603FR-07110KL; DigiKey_Part_Number 311-110KHRCT-ND
R37, R38: 1M; Manufacturer_Part_Number RC0603FR-071ML; DigiKey_Part_Number 311-1.00MHRCT-ND
R39, R40: 22R; Manufacturer_Part_Number RC2512FK-0722RL; DigiKey_Part_Number YAG3392CT-ND
SW1: POWER; Manufacturer_Part_Number EVQP7A01P; DigiKey_Part_Number P16763CT-ND
U9: LTC2954ITS8-1; Manufacturer_Part_Number LTC2954ITS8-1#TRPBF; DigiKey_Part_Number LTC2954ITS8-1#TRPBFCT-ND
U10: LM66100DCKR; SOT-363_SC-70-6; Manufacturer_Part_Number LM66100DCKR; DigiKey_Part_Number 296-53541-1-ND
U11: TPS3808G01DBVR; SOT-23-6; Manufacturer_Part_Number TPS3808G01DBVR; DigiKey_Part_Number 296-17188-1-ND
U12: 74LVC1G14GW,125; Manufacturer_Part_Number 74LVC1G14GW,125; DigiKey_Part_Number 1727-3072-1-ND

Connections:
+3V3_MCU: R20.1, R21.1, R39.2, R40.2
AON_HOLD: C55.1, C63.1, C64.1, C65.1, C66.1, C67.1, C72.1, R31.2, R34.1, U9.1 (VIN), U10.3 (~CE), U11.3 (~MR), U11.6 (VDD), U12.5 (VCC)
GND: C55.2, C56.2, C57.2, C62.2, C63.2, C64.2, C65.2, C66.2, C67.2, C68.2, C69.2, C70.2, C71.2, C72.2, D1.2 (A), Q1.2 (S), Q2.2 (S), R22.2, R33.2, R37.1, R38.1, SW1.1, U9.4 (GND), U10.2 (GND), U10.5 (ST), U11.2 (GND), U12.3 (GND)
MAIN_PWR_EN: R34.2, U9.6 (EN), U11.1 (~RESET), U12.2
unnamed: C56.1, R18.2, R19.2, U9.2 (~PB)
unnamed: C57.1, U9.7 (PDT)
unnamed: C68.1, R32.2, R33.1, U11.5 (SENSE)
unnamed: C69.1, C70.1, C71.1, U11.4 (CT)
unnamed: D1.1 (K), R19.1, SW1.2
unnamed: Q1.1 (G), R35.2, R37.2
unnamed: Q2.1 (G), R36.2, R38.2
unnamed: Q2.3 (D), R39.1, R40.1
unnamed: R31.1, U10.6 (VOUT)
POWER_BUTTON_N: R20.2, U9.5 (~INT)
POWER_KILL_N: Q1.3 (D), R21.2, R22.1, U9.8 (~KILL)
POWER_OFF_H: R35.1, R36.1, U12.4
SYS_AON: C62.1, R18.1, R32.1, U10.1 (VIN)

Notes on the sheet:
SYS-007 / PWR-006: SOURCE SUPERVISION / U11, R32-R34, C67-C71 Vtrip=Vref*(1+R32/R33)+Isense*R32. Nominal=0.405*(1+732k/100k)=3.369600V. Vref +/-2%, Isense +/-25nA; each R +/-0.1%, 25ppm/C, 100C. Corner trip=3.263705831..3.476597632V. C68: tau=(732k||100k)*1n=87.980769us (nominal). C69-C71: 3x100n C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
SYS-007 / SENS-010: HELD SUPPLY / U10, R31, C62-C66 C63-C66: 4 x 220uF/10V; Cmin=880uF*0.9^3=641.52uF. VIN=raw SYS; VOUT->R31->reservoir; CE senses reservoir. Icontrol<=1.825mA incl 1.100mA bank leakage screen. Reverse allowance=0.817mA; Itotal<=2.642mA. Vinitial=3.263705831-max(0.250,1.825mA*102.2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
SYS-007 / SENS-010: SHUTDOWN / U12, Q1-Q3, R35-R40, R70-R71 POWER_OFF_H=NOT(MAIN_PWR_EN); held-domain VCC=2.7..4.6V. Each gate branch: 1k series / 1M pulldown; 1% +100ppm/C, 100C. 4-gate peak<=4*4.6/(1000*0.99^2)=18.773595mA <50mA. Includes future USB-clear; static<=22.773595uA <100uA. VGSmin=(2.6-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
ERC supply path: U10 VOUT through R31. PWR_FLAG declares that series-fed source only; raw SYS_AON source remains unimplemented.
INCOMPLETE POWER CONTROL - NOT FOR FABRICATION PB, INT, KILL, held supply and source supervisor are connected. U12/Q1/Q2 provide fault KILL clamp and main-rail discharge. MAIN_PWR_EN feeds raw U16; held Q3 separately clamps U13 EN. SYS_AON source and USB permission-latch clear remain to be built. C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
BTN-003: POWER-KEY INPUT / R18, R19, C56, SW1 R18=10k; R19=1k; C56=100nF. SYS_AON screen=3.0..4.6V. R bounds: nominal*(0.99*0.99)..nominal*(1.01*1.01). At PB=0.6V: Isource<=(4.6-0.6)/9801 + 15uA + 12uA <435.13uA; Isink=0.6/(1020.1+0.5)>587.88uA. Thus the closed switch pulls PB below its 0.6V fallin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
BTN-004: HARDWARE FORCED-OFF TIMING / C57 C57=1uF; TDK C2012X7R1E105K125AB, 25V X7R +/-10%. C[uF]=1.56e-4*(t_added[ms]-1). t_force,nom=64ms + 1ms + 1/1.56e-4=6475.256ms (6.48s). C tolerance/temp only: 1*0.90*0.85=0.765uF; 1*1.10*1.15=1.265uF -> 4.969..8.174s using NOMINAL IC equation. Not guarantee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
