PETERFEAYEZ-PERO/Smart-Modular-adjustable-DC-PSU/PCB/USB HUP/USB Hup.kicad_pcb

## KiCad design ereader/radio_esp32.kicad_sch

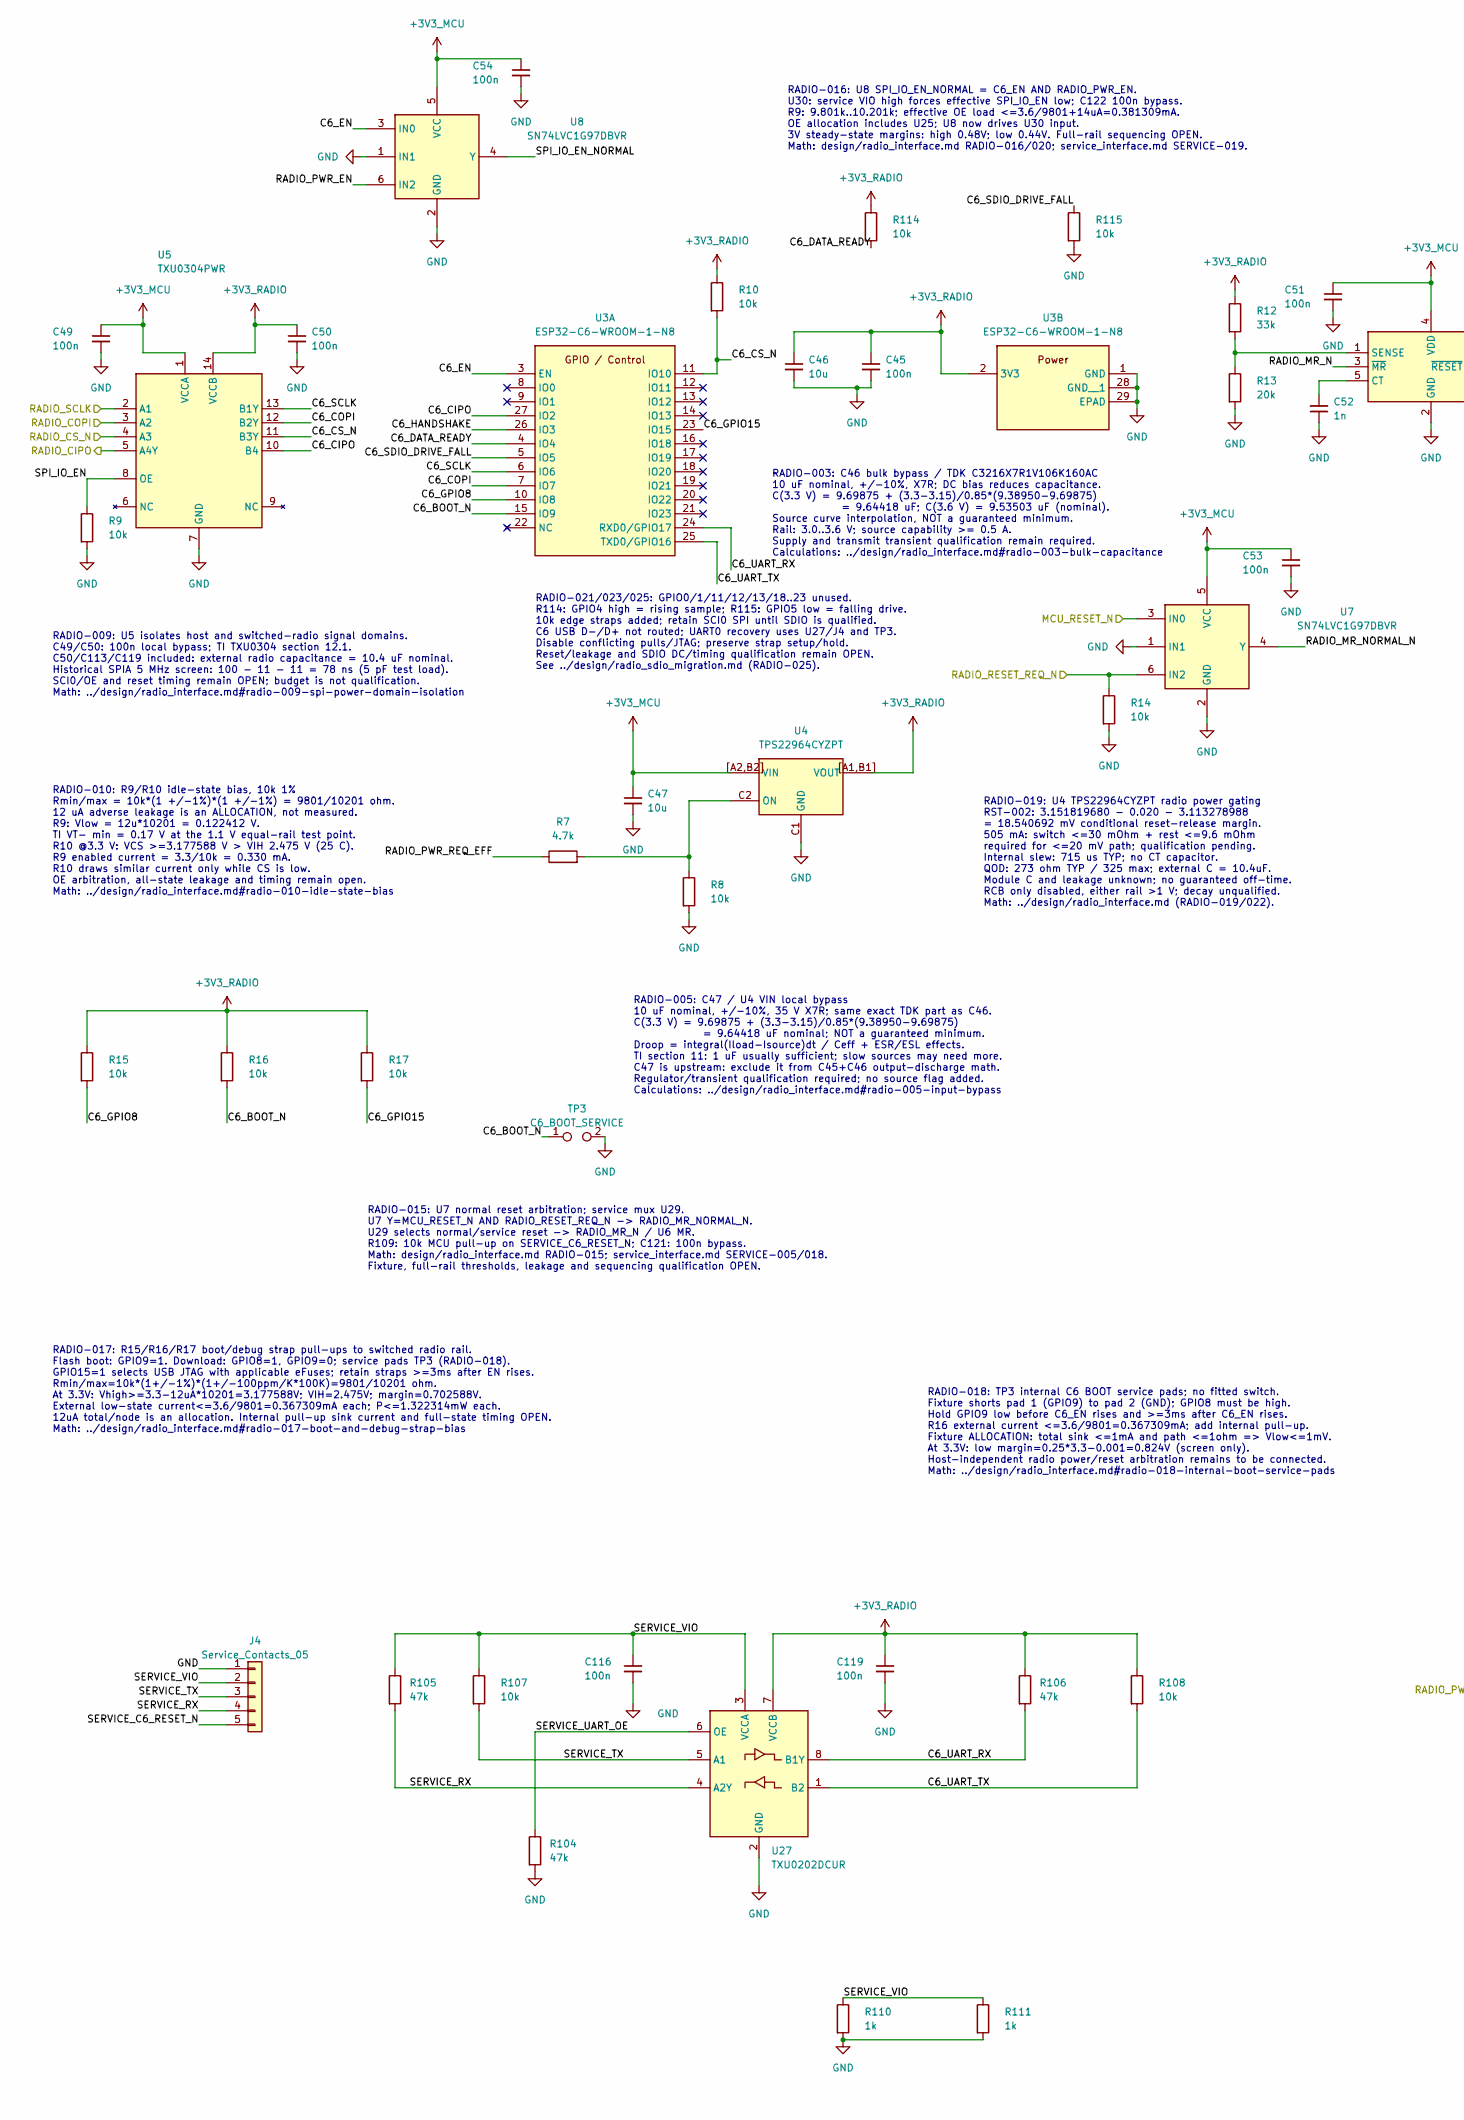
[picture p59: schematic radio_esp32.kicad_sch, part in row 1, column 1]

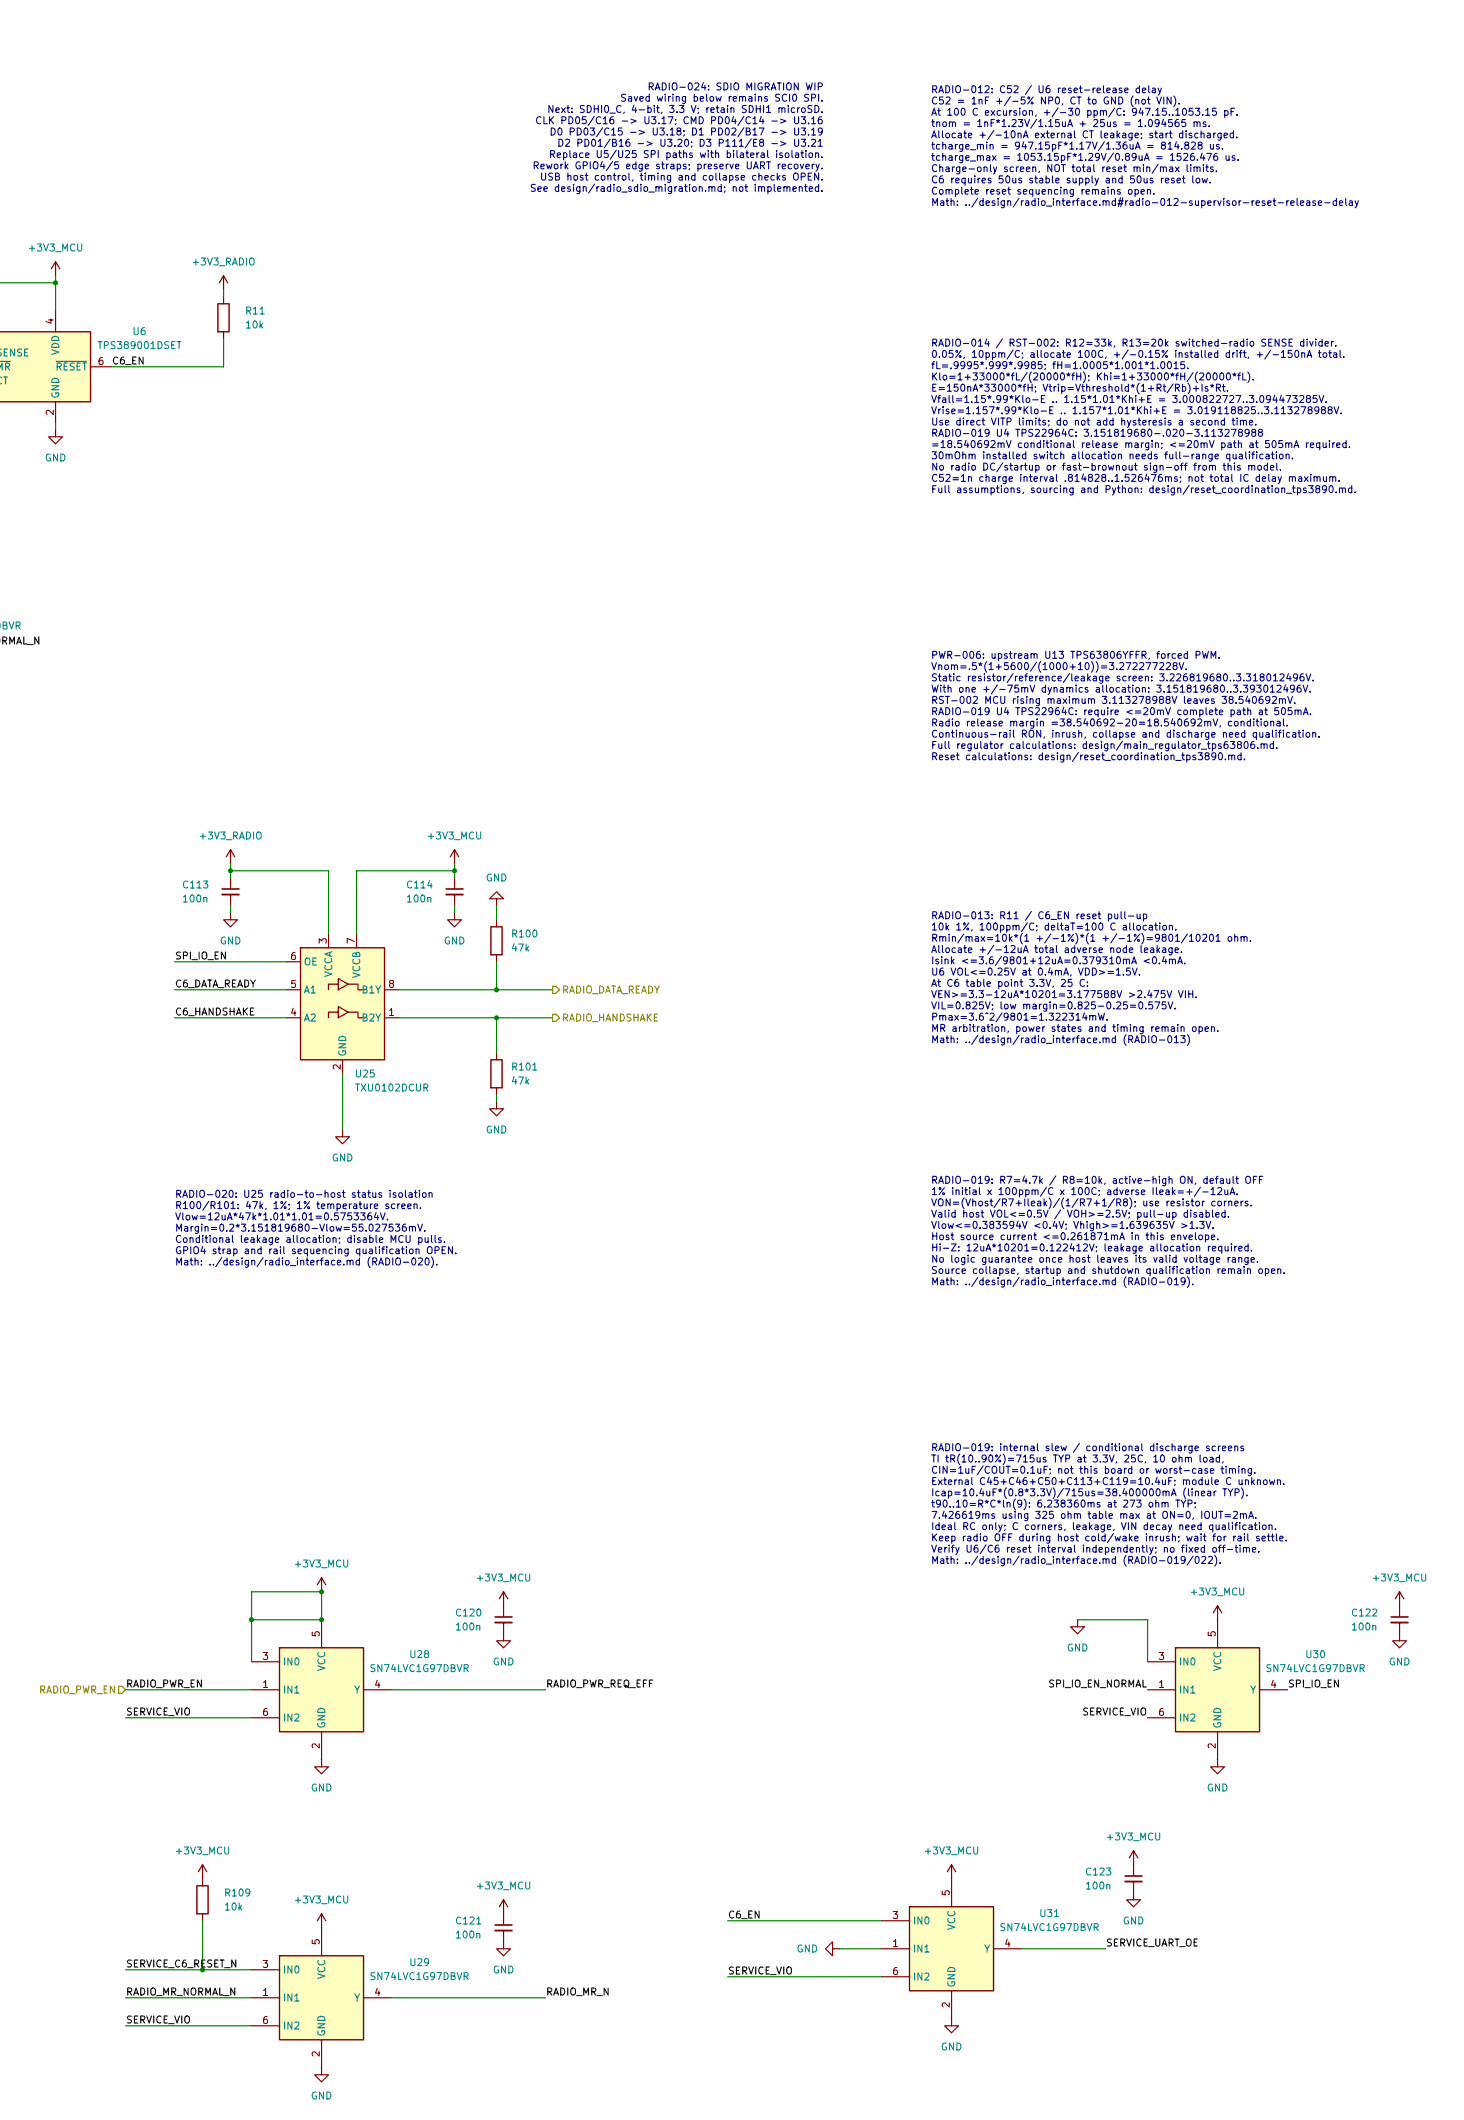
[picture p60: schematic radio_esp32.kicad_sch, part in row 1, column 2]

Parts:
C45, C49, C50, C51, C53, C54, C113, C114, C116, C119, C120, C121, C122, C123: 100n; Manufacturer_Part_Number C1608X7R1H104K080AA; DigiKey_Part_Number 445-1314-1-ND
C46, C47: 10u; Manufacturer_Part_Number C3216X7R1V106K160AC; DigiKey_Part_Number 445-14799-1-ND
C52: 1n; Manufacturer_Part_Number C1608NP01H102J080AA; DigiKey_Part_Number 445-14055-1-ND
J4: Service_Contacts_05
R7: 4.7k; Manufacturer_Part_Number RC0603FR-074K7L; DigiKey_Part_Number 311-4.70KHRCT-ND
R8, R9, R10, R11, R14, R15, R16, R17, R107, R108, R109, R114, R115: 10k; Manufacturer_Part_Number RC0603FR-0710KL; DigiKey_Part_Number 311-10.0KHRCT-ND
R12: 33k; Manufacturer_Part_Number ERA-6ARW333V; DigiKey_Part_Number P33KBSCT-ND
R13: 20k; Manufacturer_Part_Number RG1608N-203-W-T1; DigiKey_Part_Number RG16N20.0KWCT-ND
R100, R101, R104, R105, R106: 47k; Manufacturer_Part_Number RC0603FR-0747KL; DigiKey_Part_Number 311-47.0KHRCT-ND
R110, R111: 1k; Manufacturer_Part_Number RC0603FR-071KL; DigiKey_Part_Number 311-1.00KHRCT-ND
TP3: C6_BOOT_SERVICE
U3: ESP32-C6-WROOM-1-N8; XCVR_ESP32-C6-WROOM-1-N8; PARTREV 1.0; DigiKey_Part_Number 1965-ESP32-C6-WROOM-1-N8CT-ND
U4: TPS22964CYZPT; Manufacturer_Part_Number TPS22964CYZPT; DigiKey_Part_Number 296-41845-1-ND
U5: TXU0304PWR; Manufacturer_Part_Number TXU0304PWR; DigiKey_Part_Number 296-TXU0304PWRCT-ND
U6: TPS389001DSET; Manufacturer_Part_Number TPS389001DSET; DigiKey_Part_Number 296-44489-1-ND
U7, U8, U28, U29, U30, U31: SN74LVC1G97DBVR; Manufacturer_Part_Number SN74LVC1G97DBVR; DigiKey_Part_Number 296-15581-1-ND
U25: TXU0102DCUR; Manufacturer_Part_Number TXU0102DCUR; DigiKey_Part_Number 296-TXU0102DCURCT-ND
U27: TXU0202DCUR; Manufacturer_Part_Number TXU0202DCUR; DigiKey_Part_Number 296-TXU0202DCURCT-ND

Connections:
+3V3_MCU: C47.1, C49.1, C51.1, C53.1, C54.1, C114.1, C120.1, C121.1, C122.1, C123.1, R109.1, U4.[A2,B2] (VIN), U5.1 (VCCA), U6.4 (VDD), U7.5 (VCC), U8.5 (VCC), U25.7 (VCCB), U28.3 (IN0), U28.5 (VCC), U29.5 (VCC), U30.5 (VCC), U31.5 (VCC)
+3V3_RADIO: C45.1, C46.1, C50.1, C113.1, C119.1, R10.1, R11.1, R12.1, R15.1, R16.1, R17.1, R106.1, R108.1, R114.1, U3.2 (3V3), U4.[A1,B1] (VOUT), U5.14 (VCCB), U25.3 (VCCA), U27.7 (VCCB)
C6_BOOT_N: R16.2, TP3.1, U3.15 (IO9)
C6_CIPO: U3.27 (IO2), U5.10 (B4)
C6_COPI: U3.7 (IO7), U5.12 (B2Y)
C6_CS_N: R10.2, U3.11 (IO10), U5.11 (B3Y)
C6_DATA_READY: R114.2, U3.4 (IO4), U25.5 (A1)
C6_EN: R11.2, U3.3 (EN), U6.6 (~RESET), U8.3 (IN0), U31.3 (IN0)
C6_GPIO8: R15.2, U3.10 (IO8)
C6_GPIO15: R17.2, U3.23 (IO15)
C6_HANDSHAKE: U3.26 (IO3), U25.4 (A2)
C6_SCLK: U3.6 (IO6), U5.13 (B1Y)
C6_SDIO_DRIVE_FALL: R115.1, U3.5 (IO5)
C6_UART_RX: R106.2, U3.24 (RXD0/GPIO17), U27.8 (B1Y)
C6_UART_TX: R108.2, U3.25 (TXD0/GPIO16), U27.1 (B2)
GND: C45.2, C46.2, C47.2, C49.2, C50.2, C51.2, C52.1, C53.2, C54.2, C113.2, C114.2, C116.2, C119.2, C120.2, C121.2, C122.2, C123.2, J4.1 (GND), R8.2, R9.2, R13.2, R14.2, R100.1, R101.2, R104.2, R110.2, R111.2, R115.2, TP3.2, U3.1 (GND), U3.28 (GND__1), U3.29 (EPAD), U4.C1 (GND), U5.7 (GND), U6.2 (GND), U7.1 (IN1), U7.2 (GND), U8.1 (IN1), U8.2 (GND), U25.2 (GND), U27.2 (GND), U28.2 (GND), U29.2 (GND), U30.2 (GND), U30.3 (IN0), U31.1 (IN1), U31.2 (GND)
MCU_RESET_N: U7.3 (IN0)
unnamed: C52.2, U6.5 (CT)
unnamed: R7.2, R8.1, U4.C2 (ON)
unnamed: R12.2, R13.1, U6.1 (SENSE)
RADIO_CIPO: U5.5 (A4Y)
RADIO_COPI: U5.3 (A2)
RADIO_CS_N: U5.4 (A3)
RADIO_DATA_READY: R100.2, U25.8 (B1Y)
RADIO_HANDSHAKE: R101.1, U25.1 (B2Y)
RADIO_MR_N: U6.3 (~MR), U29.4 (Y)
RADIO_MR_NORMAL_N: U7.4 (Y), U29.1 (IN1)
RADIO_PWR_EN: U8.6 (IN2), U28.1 (IN1)
RADIO_PWR_REQ_EFF: R7.1, U28.4 (Y)
RADIO_RESET_REQ_N: R14.1, U7.6 (IN2)
RADIO_SCLK: U5.2 (A1)
SERVICE_C6_RESET_N: J4.5 (SERVICE_C6_RESET_N), R109.2, U29.3 (IN0)
SERVICE_RX: J4.4 (SERVICE_RX), R105.2, U27.4 (A2Y)
SERVICE_TX: J4.3 (SERVICE_TX), R107.2, U27.5 (A1)
SERVICE_UART_OE: R104.1, U27.6 (OE), U31.4 (Y)
SERVICE_VIO: C116.1, J4.2 (SERVICE_VIO), R105.1, R107.1, R110.1, R111.1, U27.3 (VCCA), U28.6 (IN2), U29.6 (IN2), U30.6 (IN2), U31.6 (IN2)
SPI_IO_EN: R9.1, U5.8 (OE), U25.6 (OE), U30.4 (Y)
SPI_IO_EN_NORMAL: U8.4 (Y), U30.1 (IN1)

Notes on the sheet:
PWR-006: upstream U13 TPS63806YFFR, forced PWM. Vnom=.5*(1+5600/(1000+10))=3.272277228V. Static resistor/reference/leakage screen: 3.226819680..3.318012496V. With one +/-75mV dynamics allocation: 3.151819680..3.393012496V. RST-002 MCU rising maximum 3.113278988V leaves 38.540692mV. RADIO-019 U4 TPS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
RADIO-013: R11 / C6_EN reset pull-up 10k 1%, 100ppm/C; deltaT=100 C allocation. Rmin/max=10k*(1 +/-1%)*(1 +/-1%)=9801/10201 ohm. Allocate +/-12uA total adverse node leakage. Isink <=3.6/9801+12uA=0.379310mA <0.4mA. U6 VOL<=0.25V at 0.4mA, VDD>=1.5V. At C6 table point 3.3V, 25 C: VEN>=3.3-12uA*10201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
RADIO-018: TP3 internal C6 BOOT service pads; no fitted switch. Fixture shorts pad 1 (GPIO9) to pad 2 (GND); GPIO8 must be high. Hold GPIO9 low before C6_EN rises and >=3ms after C6_EN rises. R16 external current <=3.6/9801=0.367309mA; add internal pull-up. Fixture ALLOCATION: total sink <=1mA and 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
RADIO-017: R15/R16/R17 boot/debug strap pull-ups to switched radio rail. Flash boot: GPIO9=1. Download: GPIO8=1, GPIO9=0; service pads TP3 (RADIO-018). GPIO15=1 selects USB JTAG with applicable eFuses; retain straps >=3ms after EN rises. Rmin/max=10k*(1+/-1%)*(1+/-100ppm/K*100K)=9801/10201 ohm. At 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
RADIO-009: U5 isolates host and switched-radio signal domains. C49/C50: 100n local bypass; TI TXU0304 section 12.1. C50/C113/C119 included: external radio capacitance = 10.4 uF nominal. Historical SPIA 5 MHz screen: 100 - 11 - 11 = 78 ns (5 pF test load). SCI0/OE and reset timing remain OPEN; budge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
RADIO-019: U4 TPS22964CYZPT radio power gating RST-002: 3.151819680 - 0.020 - 3.113278988 = 18.540692 mV conditional reset-release margin. 505 mA: switch <=30 mOhm + rest <=9.6 mOhm required for <=20 mV path; qualification pending. Internal slew: 715 us TYP; no CT capacitor. QOD: 273 ohm TYP / 325 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
RADIO-003: C46 bulk bypass / TDK C3216X7R1V106K160AC 10 uF nominal, +/-10%, X7R; DC bias reduces capacitance. C(3.3 V) = 9.69875 + (3.3-3.15)/0.85*(9.38950-9.69875) = 9.64418 uF; C(3.6 V) = 9.53503 uF (nominal). Source curve interpolation, NOT a guaranteed minimum. Rail: 3.0..3.6 V; source capabili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
RADIO-010: R9/R10 idle-state bias, 10k 1% Rmin/max = 10k*(1 +/-1%)*(1 +/-1%) = 9801/10201 ohm. 12 uA adverse leakage is an ALLOCATION, not measured. R9: Vlow = 12u*10201 = 0.122412 V. TI VT- min = 0.17 V at the 1.1 V equal-rail test point. R10 @3.3 V: VCS >=3.177588 V > VIH 2.475 V (25 C). R9 enabl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
RADIO-015: U7 normal reset arbitration; service mux U29. U7 Y=MCU_RESET_N AND RADIO_RESET_REQ_N -> RADIO_MR_NORMAL_N. U29 selects normal/service reset -> RADIO_MR_N / U6 MR. R109: 10k MCU pull-up on SERVICE_C6_RESET_N; C121: 100n bypass. Math: design/radio_interface.md RADIO-015; service_interface.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
RADIO-021/023/025: GPIO0/1/11/12/13/18..23 unused. R114: GPIO4 high = rising sample; R115: GPIO5 low = falling drive. 10k edge straps added; retain SCI0 SPI until SDIO is qualified. C6 USB D-/D+ not routed; UART0 recovery uses U27/J4 and TP3. Disable conflicting pulls/JTAG; preserve strap setup/hol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
RADIO-005: C47 / U4 VIN local bypass 10 uF nominal, +/-10%, 35 V X7R; same exact TDK part as C46. C(3.3 V) = 9.69875 + (3.3-3.15)/0.85*(9.38950-9.69875) = 9.64418 uF nominal; NOT a guaranteed minimum. Droop = integral(Iload-Isource)dt / Ceff + ESR/ESL effects. TI section 11: 1 uF usually sufficient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
RADIO-016: U8 SPI_IO_EN_NORMAL = C6_EN AND RADIO_PWR_EN. U30: service VIO high forces effective SPI_IO_EN low; C122 100n bypass. R9: 9.801k..10.201k; effective OE load <=3.6/9801+14uA=0.381309mA. OE allocation includes U25; U8 now drives U30 input. 3V steady-state margins: high 0.48V; low 0.44V. Fu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
RADIO-019: internal slew / conditional discharge screens TI tR(10..90%)=715us TYP at 3.3V, 25C, 10 ohm load, CIN=1uF/COUT=0.1uF; not this board or worst-case timing. External C45+C46+C50+C113+C119=10.4uF; module C unknown. Icap=10.4uF*(0.8*3.3V)/715us=38.400000mA (linear TYP). t90..10=R*C*ln(9): 6.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
RADIO-019: R7=4.7k / R8=10k, active-high ON, default OFF 1% initial x 100ppm/C x 100C; adverse Ileak=+/-12uA. VON=(Vhost/R7+Ileak)/(1/R7+1/R8); use resistor corners. Valid host VOL<=0.5V / VOH>=2.5V; pull-up disabled. Vlow<=0.383594V <0.4V; Vhigh>=1.639635V >1.3V. Host source current <=0.261871mA i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
RADIO-014 / RST-002: R12=33k, R13=20k switched-radio SENSE divider. 0.05%, 10ppm/C; allocate 100C, +/-0.15% installed drift, +/-150nA total. fL=.9995*.999*.9985; fH=1.0005*1.001*1.0015. Klo=1+33000*fL/(20000*fH); Khi=1+33000*fH/(20000*fL). E=150nA*33000*fH; Vtrip=Vthreshold*(1+Rt/Rb)+Is*Rt. Vfall=1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
RADIO-024: SDIO MIGRATION WIP Saved wiring below remains SCI0 SPI. Next: SDHI0_C, 4-bit, 3.3 V; retain SDHI1 microSD. CLK PD05/C16 -> U3.17; CMD PD04/C14 -> U3.16 D0 PD03/C15 -> U3.18; D1 PD02/B17 -> U3.19 D2 PD01/B16 -> U3.20; D3 P111/E8 -> U3.21 Replace U5/U25 SPI paths with bilateral isolation. 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
RADIO-020: U25 radio-to-host status isolation R100/R101: 47k, 1%; 1% temperature screen. Vlow=12uA*47k*1.01*1.01=0.5753364V. Margin=0.2*3.151819680-Vlow=55.027536mV. Conditional leakage allocation; disable MCU pulls. GPIO4 strap and rail sequencing qualification OPEN. Math: ../design/radio_interfac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
RADIO-012: C52 / U6 reset-release delay C52 = 1nF +/-5% NP0, CT to GND (not VIN). At 100 C excursion, +/-30 ppm/C: 947.15..1053.15 pF. tnom = 1nF*1.23V/1.15uA + 25us = 1.094565 ms. Allocate +/-10nA external CT leakage; start discharged. tcharge_min = 947.15pF*1.17V/1.36uA = 814.828 us. tcharge_max 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
