PETERFEAYEZ-PERO/Smart-Modular-adjustable-DC-PSU/PCB/USB HUP/USB Hup.kicad_pcb

## KiCad design ereader/sdram.kicad_sch

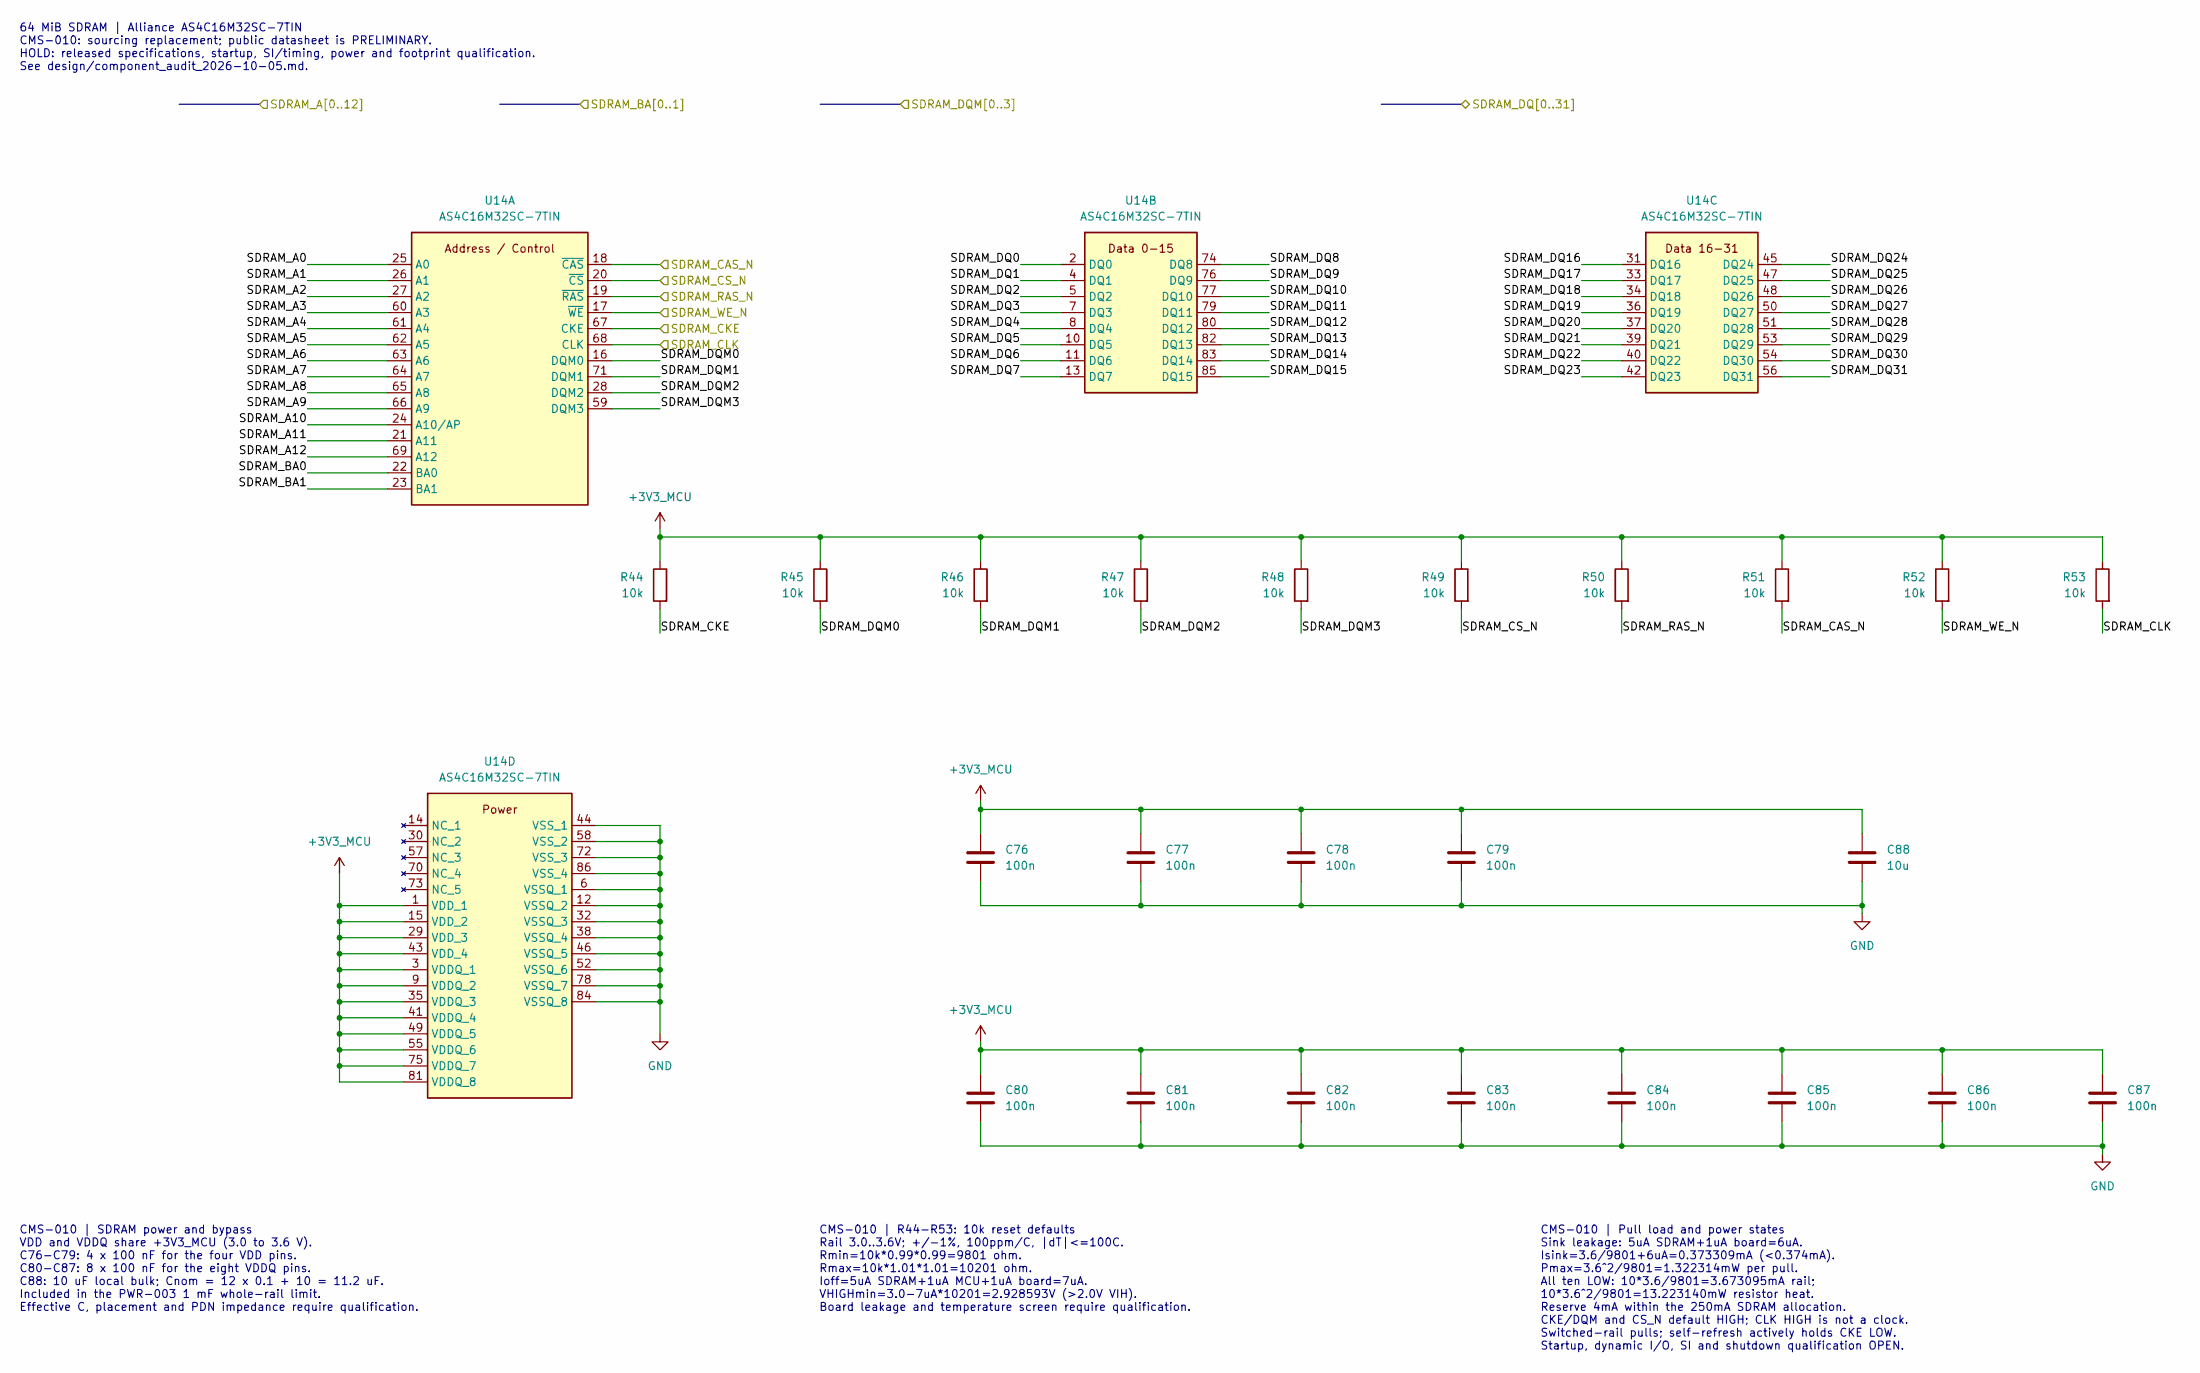
[picture p61: schematic sdram.kicad_sch]

Parts:
C76, C77, C78, C79, C80, C81, C82, C83, C84, C85, C86, C87: 100n; Manufacturer_Part_Number C1608X7R1H104K080AA; DigiKey_Part_Number 445-1314-1-ND
C88: 10u; Manufacturer_Part_Number C3216X7R1V106K160AC; DigiKey_Part_Number 445-14799-1-ND
R44, R45, R46, R47, R48, R49, R50, R51, R52, R53: 10k; Manufacturer_Part_Number RC0603FR-0710KL; DigiKey_Part_Number 311-10.0KHRCT-ND
U14: AS4C16M32SC-7TIN; Manufacturer_Part_Number AS4C16M32SC-7TIN; DigiKey_Part_Number 1450-1468-ND

Connections:
+3V3_MCU: C76.1, C77.1, C78.1, C79.1, C80.1, C81.1, C82.1, C83.1, C84.1, C85.1, C86.1, C87.1, C88.1, R44.1, R45.1, R46.1, R47.1, R48.1, R49.1, R50.1, R51.1, R52.1, R53.1, U14.1 (VDD_1), U14.3 (VDDQ_1), U14.9 (VDDQ_2), U14.15 (VDD_2), U14.29 (VDD_3), U14.35 (VDDQ_3), U14.41 (VDDQ_4), U14.43 (VDD_4), U14.49 (VDDQ_5), U14.55 (VDDQ_6), U14.75 (VDDQ_7), U14.81 (VDDQ_8)
GND: C76.2, C77.2, C78.2, C79.2, C80.2, C81.2, C82.2, C83.2, C84.2, C85.2, C86.2, C87.2, C88.2, U14.6 (VSSQ_1), U14.12 (VSSQ_2), U14.32 (VSSQ_3), U14.38 (VSSQ_4), U14.44 (VSS_1), U14.46 (VSSQ_5), U14.52 (VSSQ_6), U14.58 (VSS_2), U14.72 (VSS_3), U14.78 (VSSQ_7), U14.84 (VSSQ_8), U14.86 (VSS_4)
SDRAM_A0: U14.25 (A0)
SDRAM_A1: U14.26 (A1)
SDRAM_A2: U14.27 (A2)
SDRAM_A3: U14.60 (A3)
SDRAM_A4: U14.61 (A4)
SDRAM_A5: U14.62 (A5)
SDRAM_A6: U14.63 (A6)
SDRAM_A7: U14.64 (A7)
SDRAM_A8: U14.65 (A8)
SDRAM_A9: U14.66 (A9)
SDRAM_A10: U14.24 (A10/AP)
SDRAM_A11: U14.21 (A11)
SDRAM_A12: U14.69 (A12)
SDRAM_BA0: U14.22 (BA0)
SDRAM_BA1: U14.23 (BA1)
SDRAM_CAS_N: R51.2, U14.18 (~CAS)
SDRAM_CKE: R44.2, U14.67 (CKE)
SDRAM_CLK: R53.2, U14.68 (CLK)
SDRAM_CS_N: R49.2, U14.20 (~CS)
SDRAM_DQ0: U14.2 (DQ0)
SDRAM_DQ1: U14.4 (DQ1)
SDRAM_DQ2: U14.5 (DQ2)
SDRAM_DQ3: U14.7 (DQ3)
SDRAM_DQ4: U14.8 (DQ4)
SDRAM_DQ5: U14.10 (DQ5)
SDRAM_DQ6: U14.11 (DQ6)
SDRAM_DQ7: U14.13 (DQ7)
SDRAM_DQ8: U14.74 (DQ8)
SDRAM_DQ9: U14.76 (DQ9)
SDRAM_DQ10: U14.77 (DQ10)
SDRAM_DQ11: U14.79 (DQ11)
SDRAM_DQ12: U14.80 (DQ12)
SDRAM_DQ13: U14.82 (DQ13)
SDRAM_DQ14: U14.83 (DQ14)
SDRAM_DQ15: U14.85 (DQ15)
SDRAM_DQ16: U14.31 (DQ16)
SDRAM_DQ17: U14.33 (DQ17)
SDRAM_DQ18: U14.34 (DQ18)
SDRAM_DQ19: U14.36 (DQ19)
SDRAM_DQ20: U14.37 (DQ20)
SDRAM_DQ21: U14.39 (DQ21)
SDRAM_DQ22: U14.40 (DQ22)
SDRAM_DQ23: U14.42 (DQ23)
SDRAM_DQ24: U14.45 (DQ24)
SDRAM_DQ25: U14.47 (DQ25)
SDRAM_DQ26: U14.48 (DQ26)
SDRAM_DQ27: U14.50 (DQ27)
SDRAM_DQ28: U14.51 (DQ28)
SDRAM_DQ29: U14.53 (DQ29)
SDRAM_DQ30: U14.54 (DQ30)
SDRAM_DQ31: U14.56 (DQ31)
SDRAM_DQM0: R45.2, U14.16 (DQM0)
SDRAM_DQM1: R46.2, U14.71 (DQM1)
SDRAM_DQM2: R47.2, U14.28 (DQM2)
SDRAM_DQM3: R48.2, U14.59 (DQM3)
SDRAM_RAS_N: R50.2, U14.19 (~RAS)
SDRAM_WE_N: R52.2, U14.17 (~WE)

Notes on the sheet:
CMS-010 | SDRAM power and bypass VDD and VDDQ share +3V3_MCU (3.0 to 3.6 V). C76-C79: 4 x 100 nF for the four VDD pins. C80-C87: 8 x 100 nF for the eight VDDQ pins. C88: 10 uF local bulk; Cnom = 12 x 0.1 + 10 = 11.2 uF. Included in the PWR-003 1 mF whole-rail limit. Effective C, placement and PDN i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
CMS-010 | Pull load and power states Sink leakage: 5uA SDRAM+1uA board=6uA. Isink=3.6/9801+6uA=0.373309mA (<0.374mA). Pmax=3.6^2/9801=1.322314mW per pull. All ten LOW: 10*3.6/9801=3.673095mA rail; 10*3.6^2/9801=13.223140mW resistor heat. Reserve 4mA within the 250mA SDRAM allocation. CKE/DQM and CS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
CMS-010 | R44-R53: 10k reset defaults Rail 3.0..3.6V; +/-1%, 100ppm/C, |dT|<=100C. Rmin=10k*0.99*0.99=9801 ohm. Rmax=10k*1.01*1.01=10201 ohm. Ioff=5uA SDRAM+1uA MCU+1uA board=7uA. VHIGHmin=3.0-7uA*10201=2.928593V (>2.0V VIH). Board leakage and temperature screen require qualification.
64 MiB SDRAM | Alliance AS4C16M32SC-7TIN CMS-010: sourcing replacement; public datasheet is PRELIMINARY. HOLD: released specifications, startup, SI/timing, power and footprint qualification. See design/component_audit_2026-10-05.md.
