PETERFEAYEZ-PERO/Smart-Modular-adjustable-DC-PSU/PCB/USB HUP/USB Hup.kicad_pcb

## KiCad design ereader/user_controls.kicad_sch

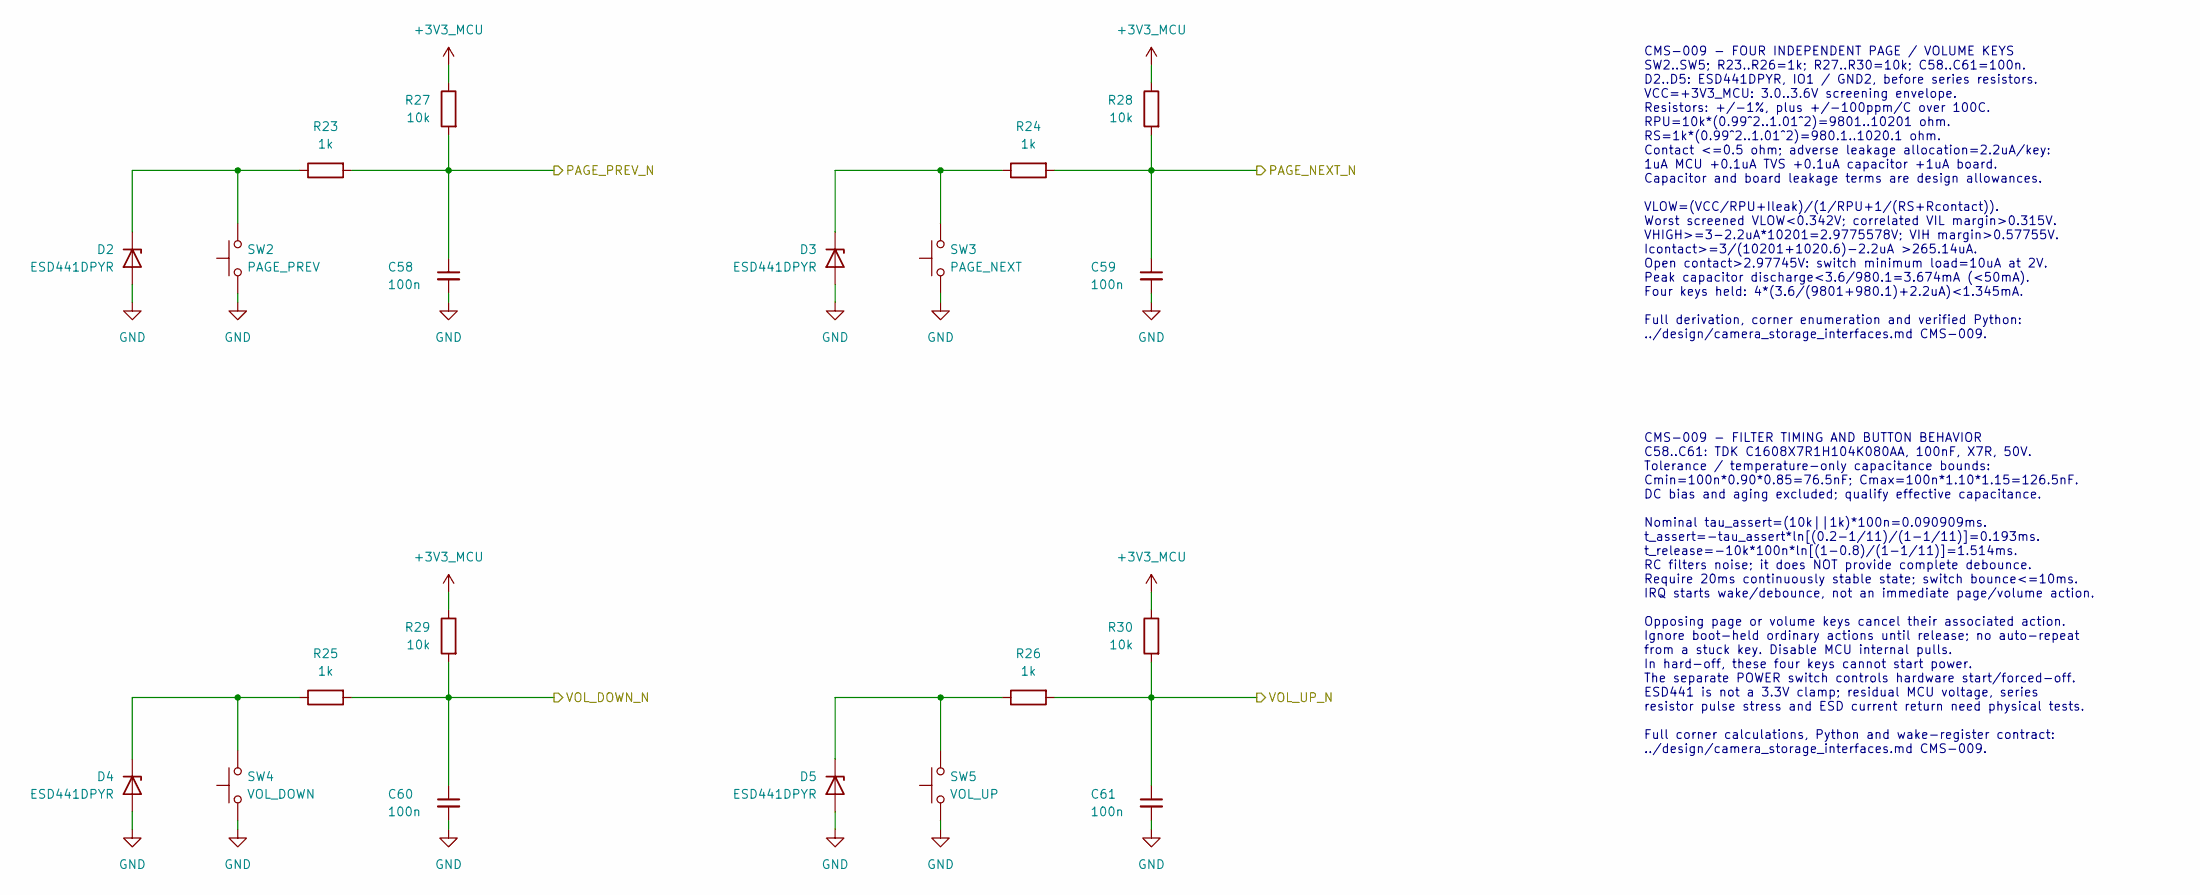
[picture p62: schematic user_controls.kicad_sch]

Parts:
C58, C59, C60, C61: 100n; Manufacturer_Part_Number C1608X7R1H104K080AA; DigiKey_Part_Number 445-1314-1-ND
D2, D3, D4, D5: ESD441DPYR; Manufacturer_Part_Number ESD441DPYR; DigiKey_Part_Number 296-ESD441DPYRCT-ND
R23, R24, R25, R26: 1k; Manufacturer_Part_Number RC0603FR-071KL; DigiKey_Part_Number 311-1.00KHRCT-ND
R27, R28, R29, R30: 10k; Manufacturer_Part_Number RC0603FR-0710KL; DigiKey_Part_Number 311-10.0KHRCT-ND
SW2: PAGE_PREV; Manufacturer_Part_Number EVQP7A01P; DigiKey_Part_Number P16763CT-ND
SW3: PAGE_NEXT; Manufacturer_Part_Number EVQP7A01P; DigiKey_Part_Number P16763CT-ND
SW4: VOL_DOWN; Manufacturer_Part_Number EVQP7A01P; DigiKey_Part_Number P16763CT-ND
SW5: VOL_UP; Manufacturer_Part_Number EVQP7A01P; DigiKey_Part_Number P16763CT-ND

Connections:
+3V3_MCU: R27.1, R28.1, R29.1, R30.1
GND: C58.2, C59.2, C60.2, C61.2, D2.2 (A), D3.2 (A), D4.2 (A), D5.2 (A), SW2.1, SW3.1, SW4.1, SW5.1
unnamed: D2.1 (K), R23.1, SW2.2
unnamed: D3.1 (K), R24.1, SW3.2
unnamed: D4.1 (K), R25.1, SW4.2
unnamed: D5.1 (K), R26.1, SW5.2
PAGE_NEXT_N: C59.1, R24.2, R28.2
PAGE_PREV_N: C58.1, R23.2, R27.2
VOL_DOWN_N: C60.1, R25.2, R29.2
VOL_UP_N: C61.1, R26.2, R30.2

Notes on the sheet:
CMS-009 - FOUR INDEPENDENT PAGE / VOLUME KEYS SW2..SW5; R23..R26=1k; R27..R30=10k; C58..C61=100n. D2..D5: ESD441DPYR, IO1 / GND2, before series resistors. VCC=+3V3_MCU: 3.0..3.6V screening envelope. Resistors: +/-1%, plus +/-100ppm/C over 100C. RPU=10k*(0.99^2..1.01^2)=9801..10201 ohm. RS=1k*(0.99^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
CMS-009 - FILTER TIMING AND BUTTON BEHAVIOR C58..C61: TDK C1608X7R1H104K080AA, 100nF, X7R, 50V. Tolerance / temperature-only capacitance bounds: Cmin=100n*0.90*0.85=76.5nF; Cmax=100n*1.10*1.15=126.5nF. DC bias and aging excluded; qualify effective capacitance. Nominal tau_assert=(10k||1k)*100n=0.09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
